zengwangfa/Smart-Hive/software/node-2019.10.29/docs/A Low-Power CoAP for Contiki.ppt.pdf

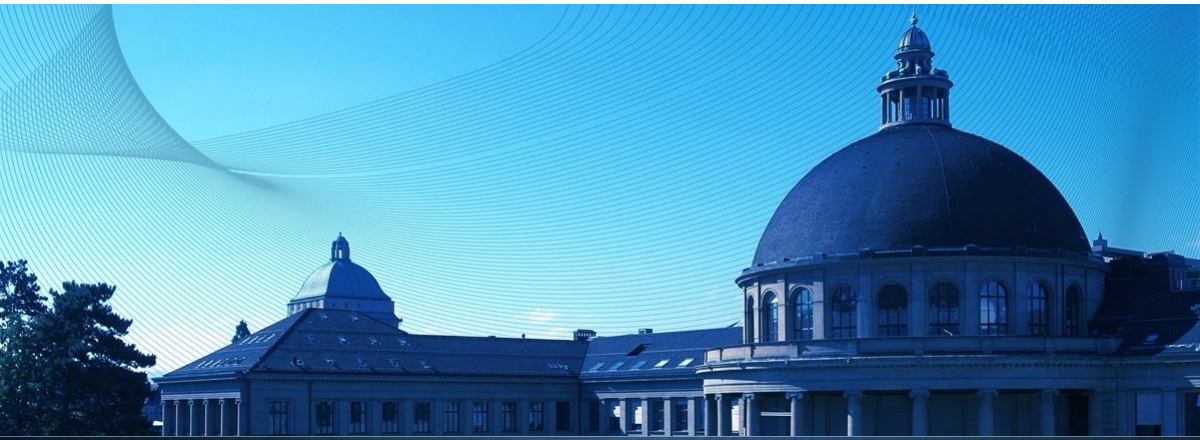
[picture p32: figure]

Monday, 17 Oct 2011

# A Low-Power CoAP for Contiki

### Matthias Kovatsch, Simon Duquennoy, and Adam Dunkels

kovatsch@inf.ethz.ch | simonduq@sics.se | adam@sics.se

Matthias Kovatsch – ETH Zürich | A Low-Power CoAP for Contiki

## Internet of Things Protocol Stack

Layer | Protocol

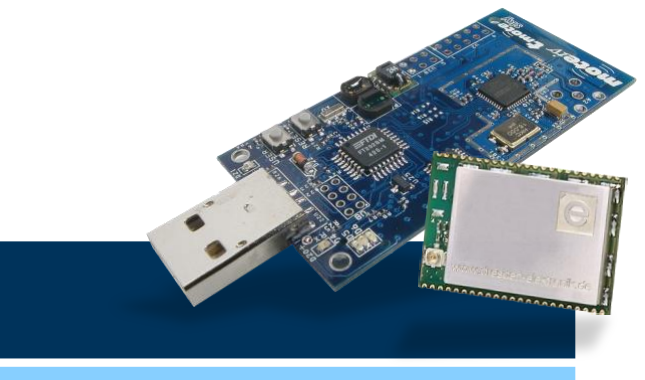
[picture p33: figure]

Application | CoAP / REST Engine (Erbium)
Transport | UDP
Network | IPv6 / RPL
Adaption | 6LoWPAN
MAC | CSMA / link-layer bursts / link-layer bursts
Radio Duty Cycling | ContikiMAC
Physical | IEEE 802.15.4

## ContikiMAC

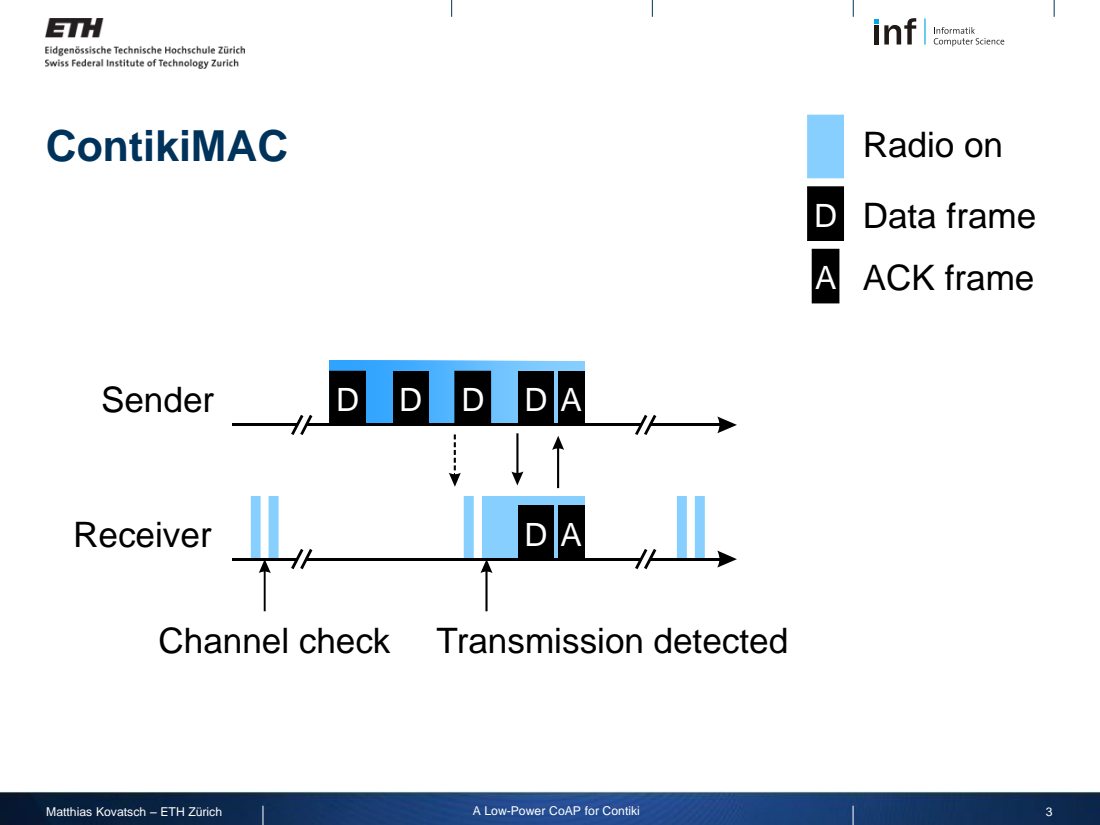
[picture p34: page 3]
ACK frame; Data frame; Radio on; Sender; Receiver; Transmission detected; Channel check

## Link-layer Bursts

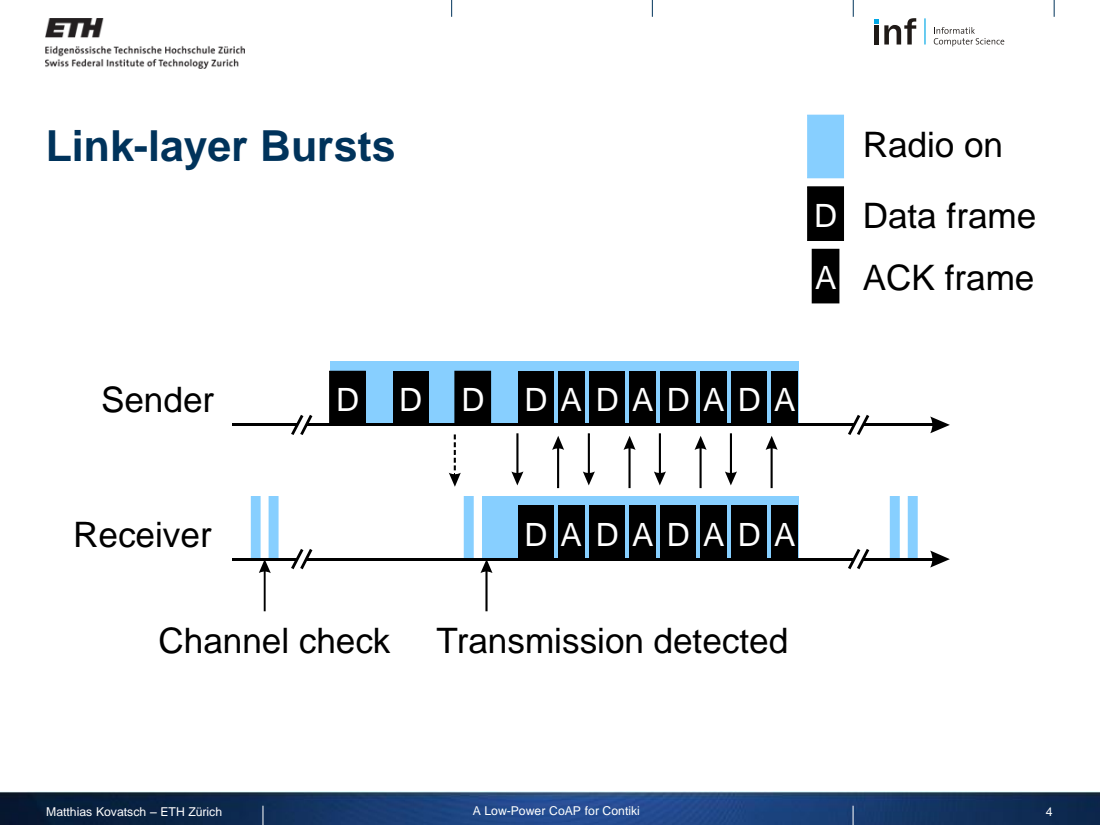
[picture p35: page 4]
Sender; Receiver; Transmission detected; Channel check; A ACK frame; Data frame; Radio on

## Constrained Application Protocol (CoAP)

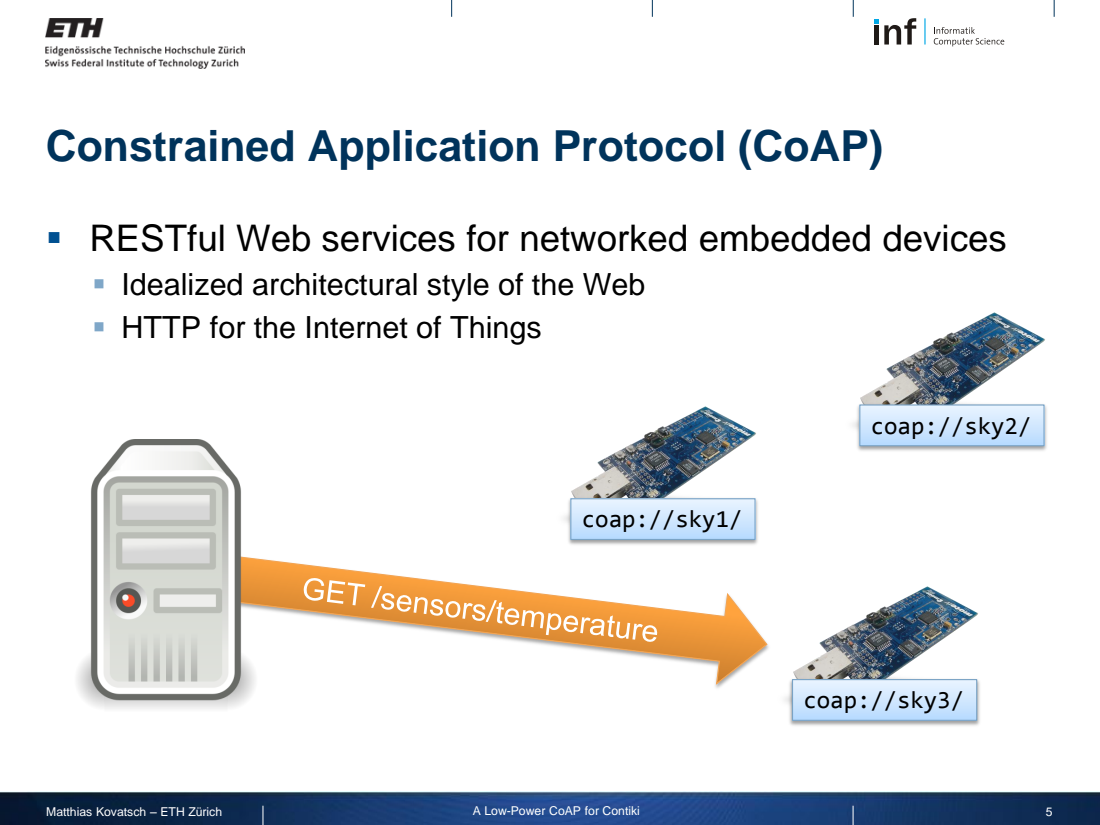
[picture p36: page 5]
coap://sky3/; coap://sky2/; coap://sky1/

▪ RESTful Web services for networked embedded devices
▪ Idealized architectural style of the Web
▪ HTTP for the Internet of Things

## «Erbium» CoAP for Contiki

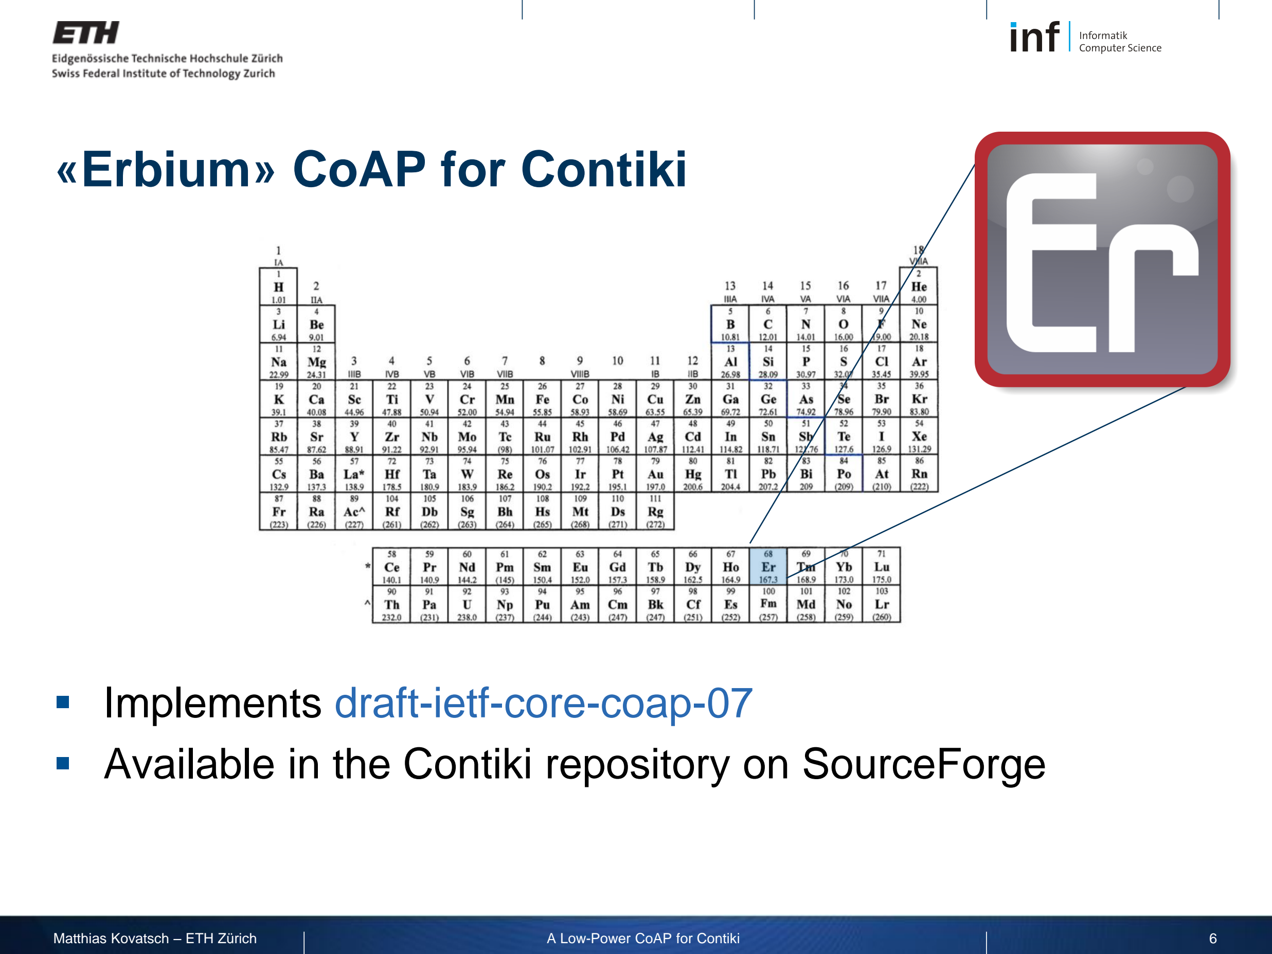
[picture p37: page 6]

### - Implements draft-ietf-core-coap-07 - Available in the Contiki repository on SourceForge

## «Erbium» CoAP

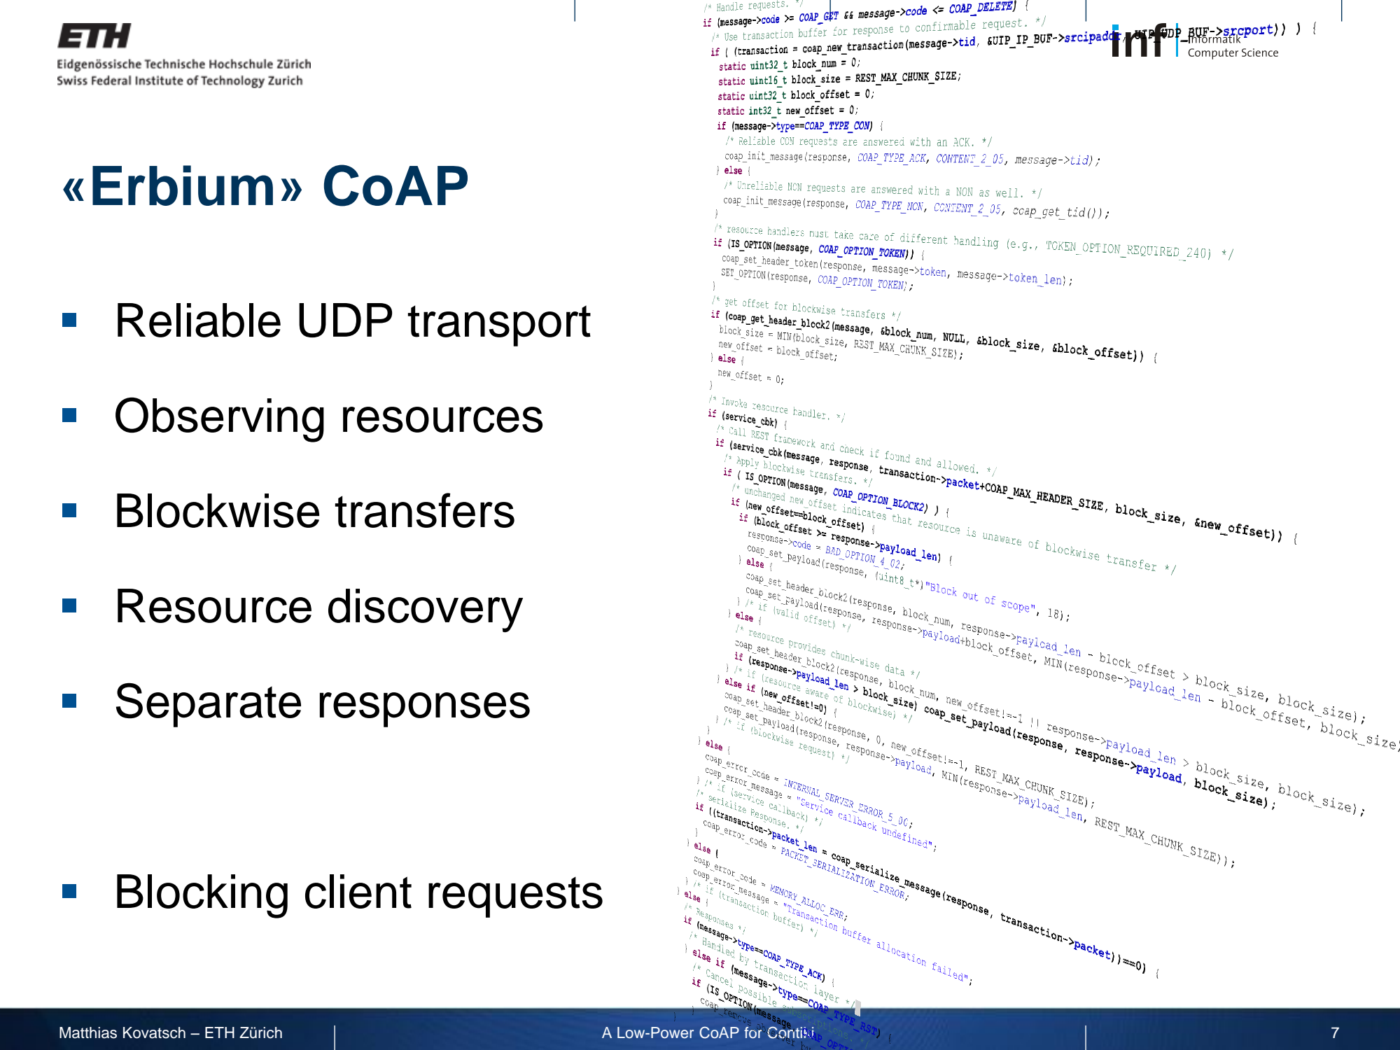
[picture p38: page 7]

### - Reliable UDP transport

### - Observing resources

### - Blockwise transfers

### - Resource discovery

### - Separate responses

### - Blocking client requests

## «Erbium» REST Engine

### - Resource abstraction

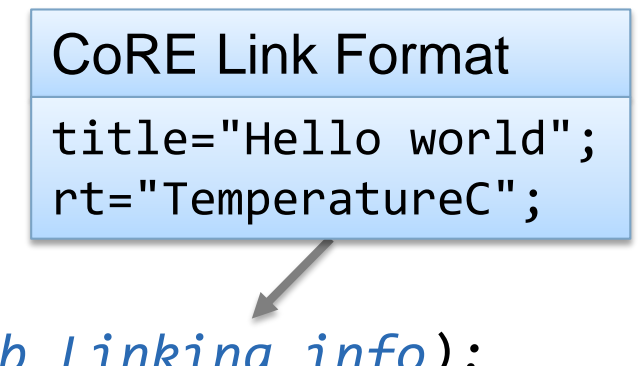
[picture p39: figure]
CoRE Link Format; title="Hello world"; rt="TemperatureC";

RESOURCE(handle, METHODs, URI-Path, Web Linking info);
- Resource handler

PERIODIC_RESOURCE(handle, METHODs, URI-Path, info, period);
- Additional periodic handler

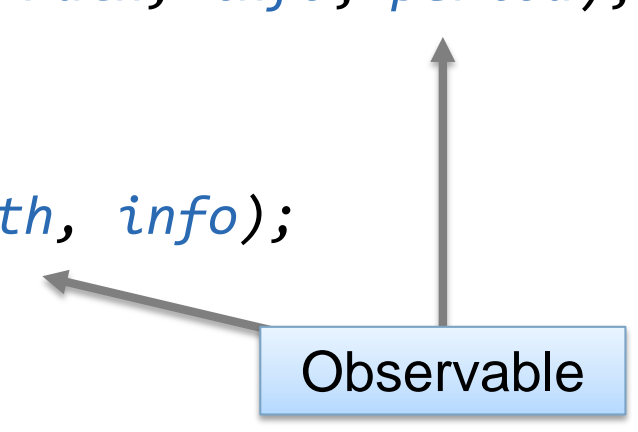
[picture p40: figure]
Observable

EVENT_RESOURCE(handle, METHODs, URI-Path, info);
- Additional event handler

## «Erbium» Memory Footprint

| ROM [kB] | RAM [kB]
CoAP REST Engine total | 8.5 | 1.5
Measured stack usage | – | 0.1
REST Engine | 0.7 | 0
CoAP-07 base | 4.5 | 0
CoAP-07 server | 1.9 | 0.3
CoAP-07 transport | 0.4 | 0.9
CoAP-07 observing | 0.9 | 0.2
CoAP-07 separate | 0.1 | 0

## Experimental Set-up

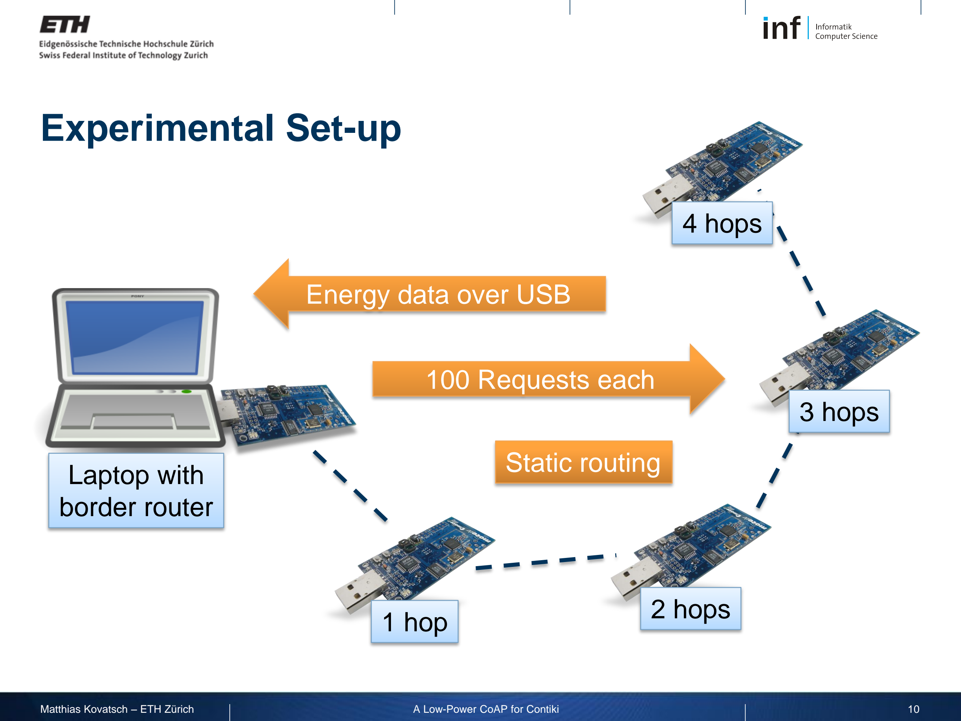
[picture p41: page 10]

3 hops

2 hops 1 hop

Energy data over USB

100 Requests each

Laptop with
border router

Static routing

4 hops

## Energy vs Latency for 64B Payload

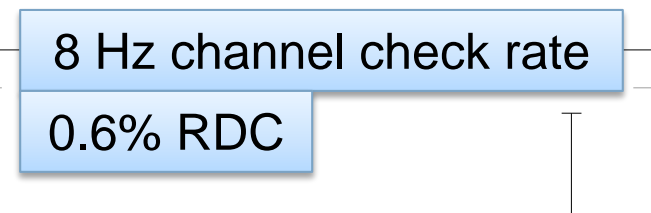
[picture p42: figure]
8 Hz channel check rate; 0.6% RDC

Number of hops | Number of hops

Energy [mJ]
Latency [s]

No duty cycling
ContikiMAC
1 | 2 | 3 | 4

0

100

200

300

400

1 | 2 | 3 | 4

0

0.2

0.4

0.6

0.8

1.0

## Transmitting Large Data

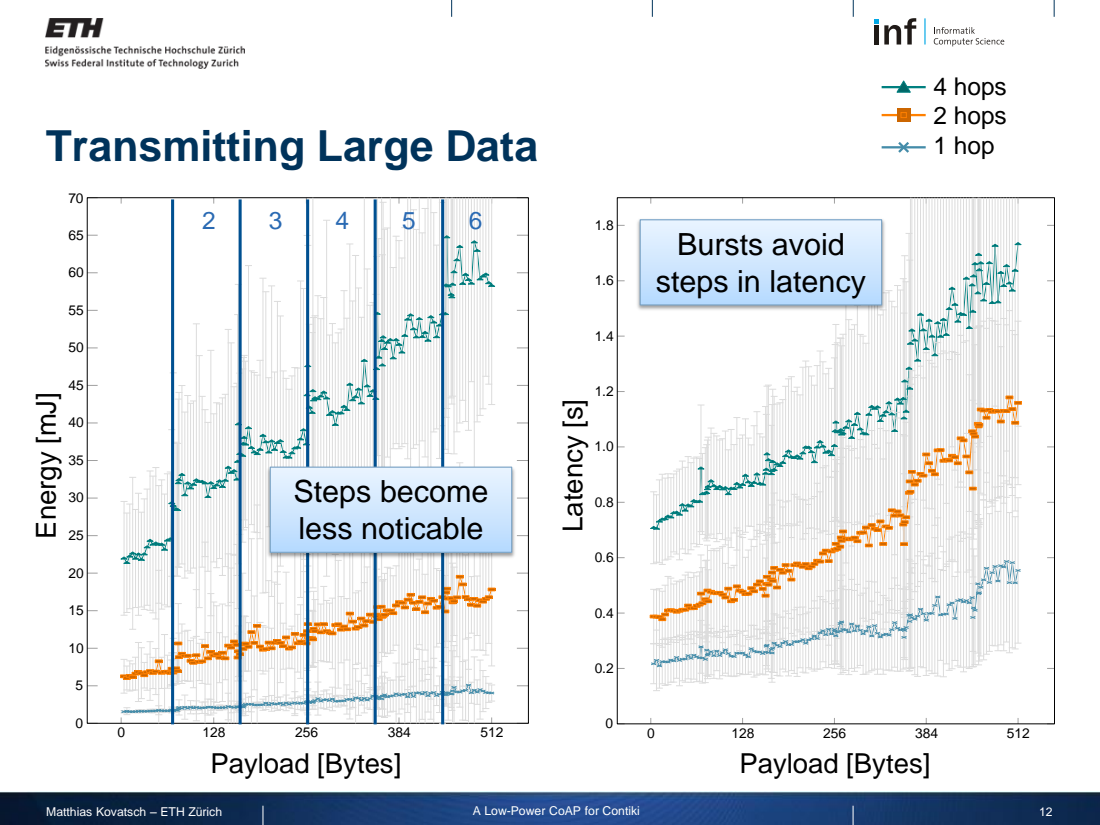
[picture p43: page 12]
Payload [Bytes]; Energy [mJ]; Latency [s]; Steps become less noticable; 4 hops 2 hops 1 hop

Bursts avoid
steps in latency

## Transmitting Large Data

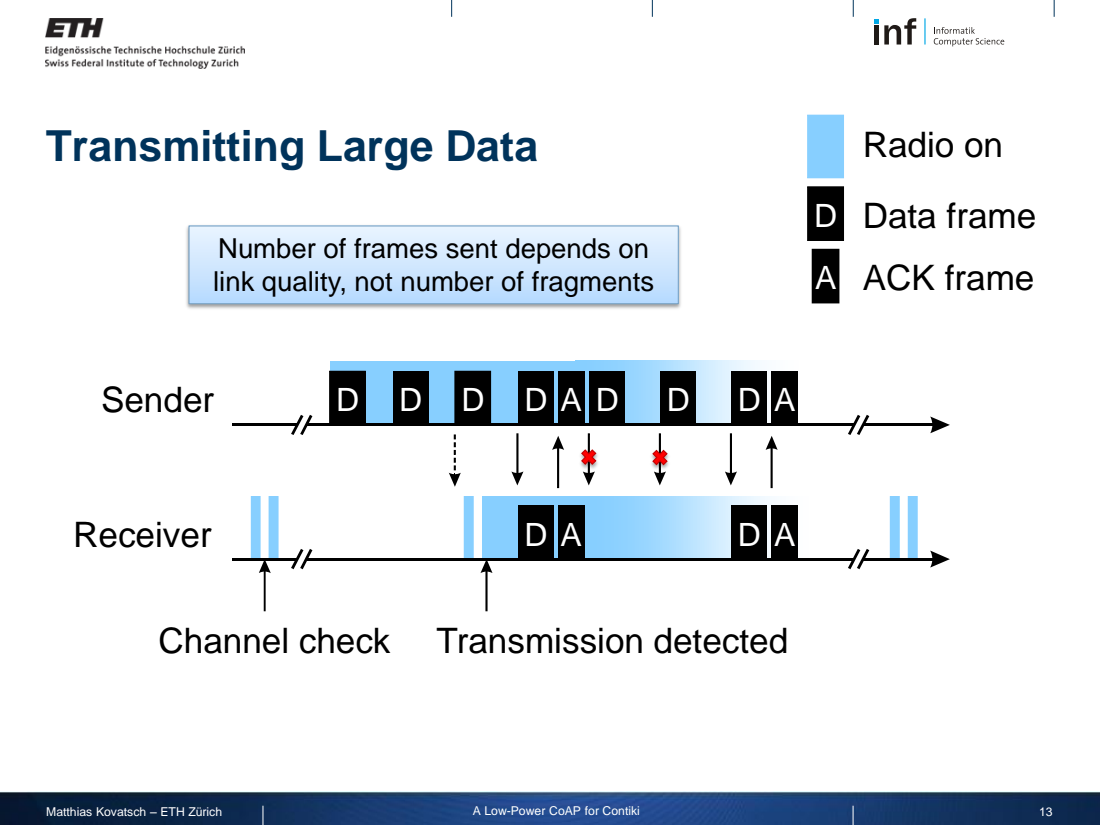
[picture p44: page 13]
Sender; Receiver; Transmission detected; Channel check; A ACK frame; Data frame; Radio on

Number of frames sent depends on
link quality, not number of fragments

## Separate Responses

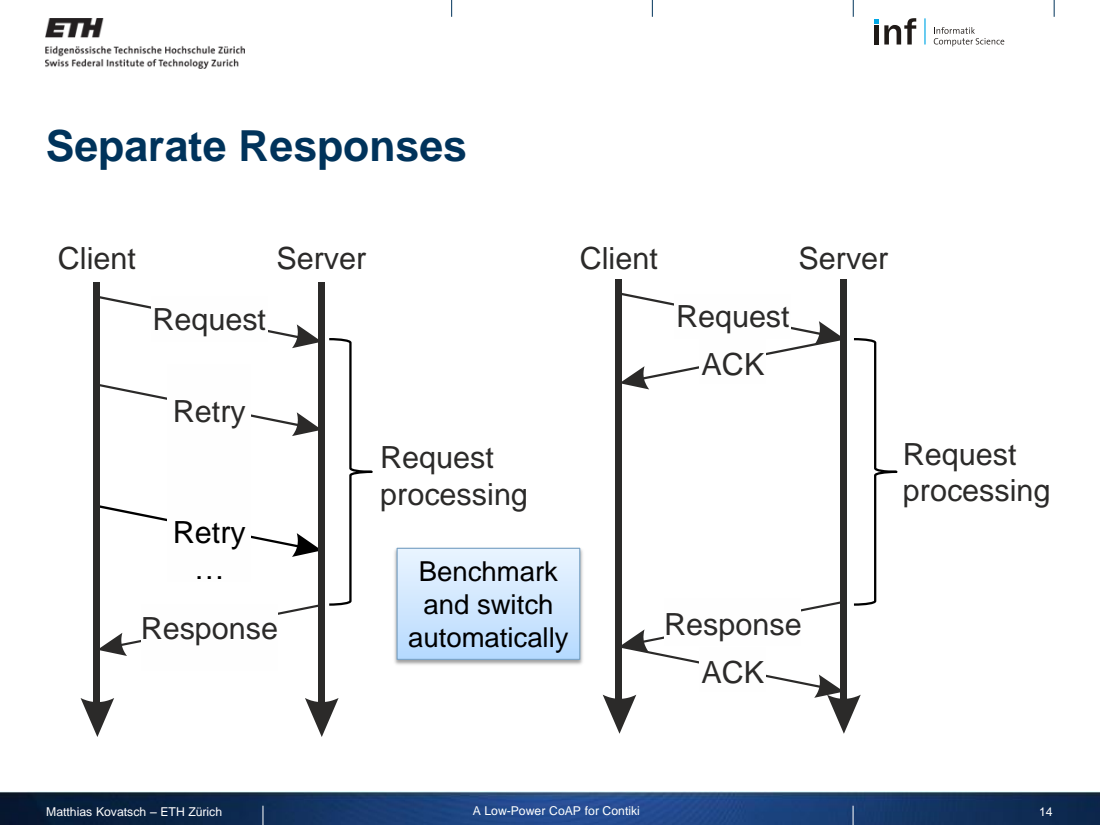
[picture p45: page 14]
Client; Server; Request processing; Request; Retry; Retry …; Response; ACK; Benchmark and switch automatically

## Separate Responses over 4 Hops

Without
With

Energy [mJ]

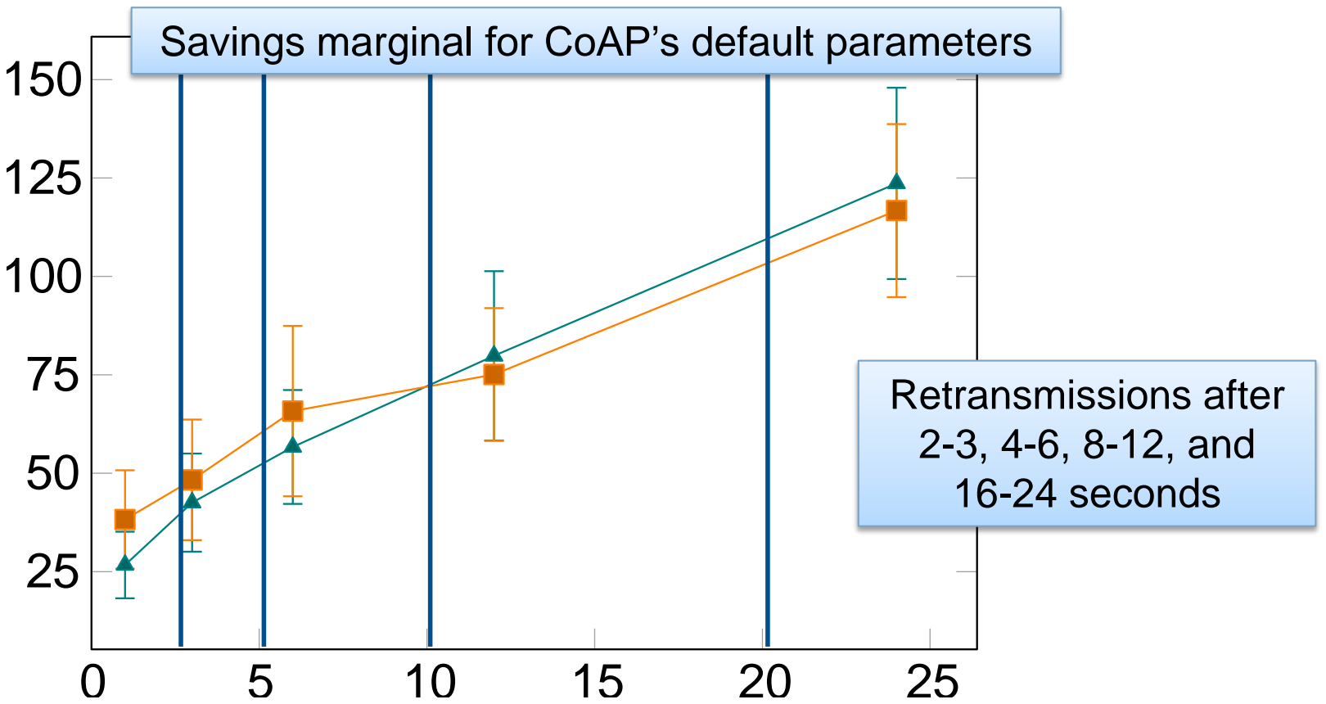
[picture p46: figure]
Retransmissions after 2-3, 4-6, 8-12, and 16-24 seconds

Server processing time [s]

Savings marginal for CoAP’s default parameters

## Conclusion

### - Internet of Things stack

- Isolated layers with different goals work together
- Layered architecture lowers complexity
- Optimize for single fragments
- No need to optimize payload size once fragmented

### - CoAP

- Draft 07 implementation for Contiki
- Block size most important parameter for memory-constrained devices: Exponential sizes too coarse-grained

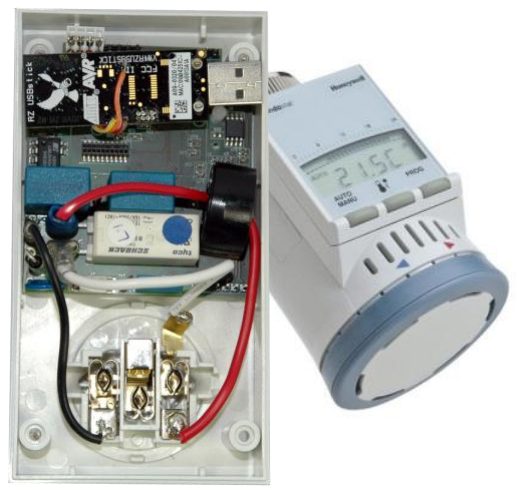
[picture p47: figure]

## Future Work

### - Extend «Erbium» CoAP

- Blocking resource handler for UART
- Hierarchical resources / URI-Path handling
- Improve observer handling (only one buffer)

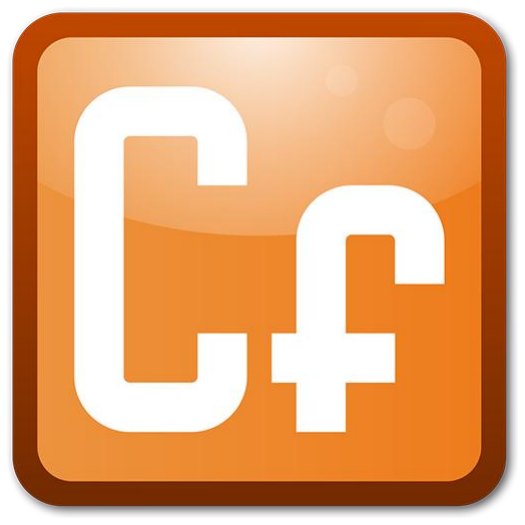
[picture p48: figure]

### - Study RESTful approach

- Long-term deployment with smart appliances
- Separate application logic from device firmware and combine with «Californium»-based App Server

https://github.com/mkovatsc/Californium

## THANK YOU

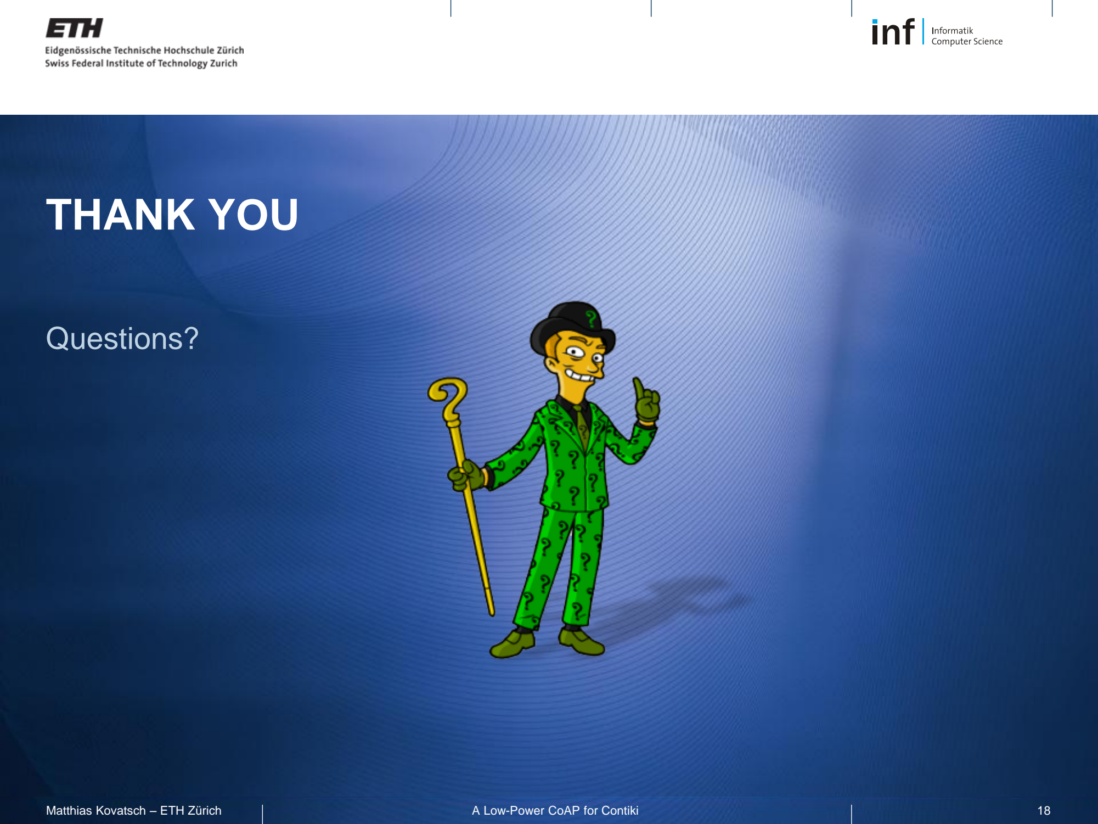
[picture p49: page 18]

Questions?

## Blockwise Transfers

### Automatic or controlled by handler

RESOURCE(handle, METHODs, URI-Path, Web Linking info);
- Resource handler

handle_handler(void* request, void* response,
uint8_t *buffer, uint16_t preferred_size, int32_t *offset);

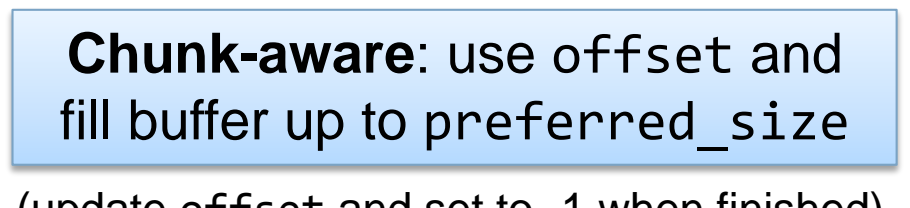
[picture p50: figure]
Chunk-aware: use offset and fill buffer up to preferred_size
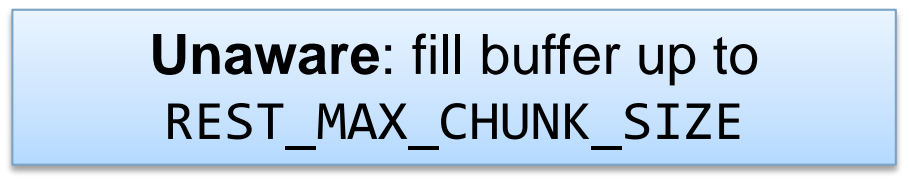
[picture p51: figure]
Unaware: fill buffer up to REST_MAX_CHUNK_SIZE

(update offset and set to -1 when finished)

## Observing Resources

### Post-handler registers observers automatically

PERIODIC_RESOURCE(handle, METHODs, URI-Path, info, period);
- Additional periodic handler

EVENT_RESOURCE(handle, METHODs, URI-Path, info);
- Additional event handler

int handle_event_handler(resource_t *r) {
REST.notify_subscribers(r->url, CON/NON, seqno, buf, len); }

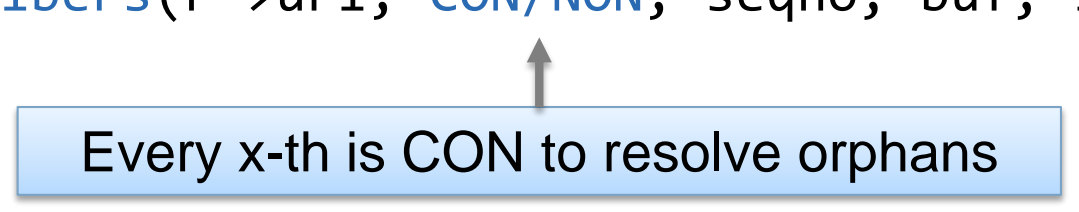
[picture p52: figure]
Every x-th is CON to resolve orphans

## «Erbium» REST Engine

### - Manipulate messages with REST API

- REST.set_header_etag(response, etag_buf, etag_len);
- REST.get_query_variable(request, name, value_buffer);

### - Link implementation

- coap-03
- coap-06
- coap-07
- …
- HTTP (not yet implemented for Erbium)
