zengwangfa/Smart-Hive/docs/网关使用说明/蜂箱网关使用简要说明.pdf

网关设备使用简要说明

## 一、供电

供电注意：使用5V电源适配器供电

## 二、联网

在网关设备网口处出入可直接上网的网线即可

## 三、使用方法

将网关部署在距离蜂箱节点附近，即可让蜂箱
节点自动上传数据至服务器，并可下行控制蜂
箱节点执行相应动作。

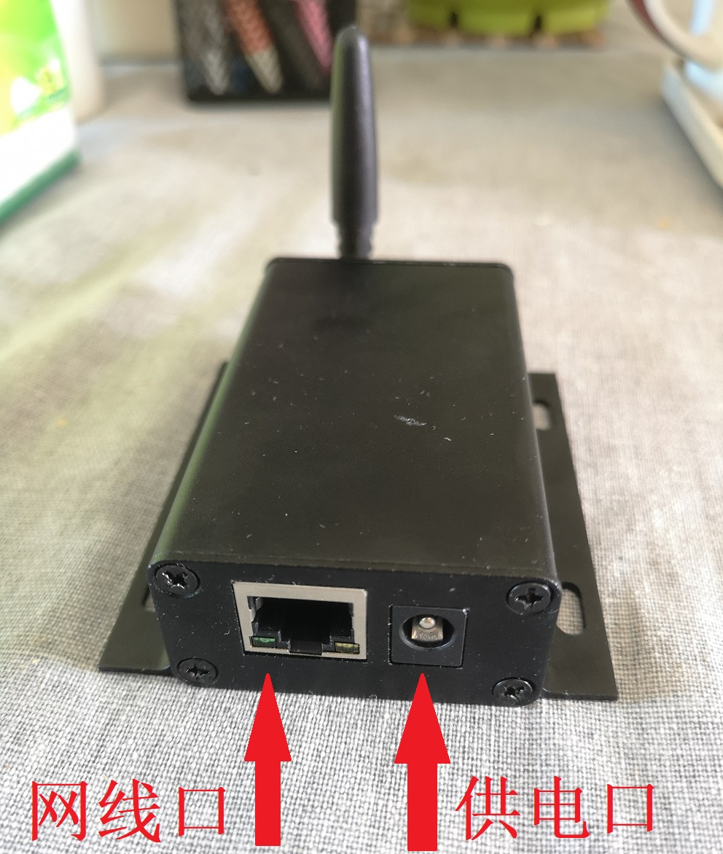
[picture p64: figure]
