zengwangfa/Smart-Hive/docs/pictures/uboot.png

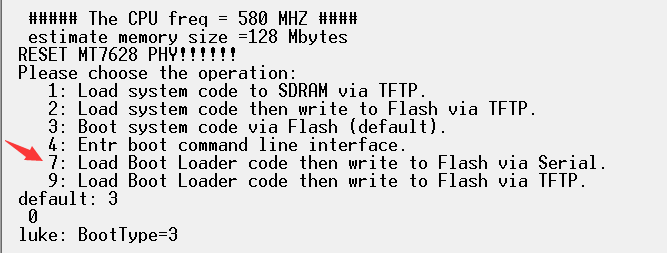
docs/pictures/uboot.png
