zengwangfa/Smart-Hive/new_node/bsp/stm32/docs/figures/adc_config3.png

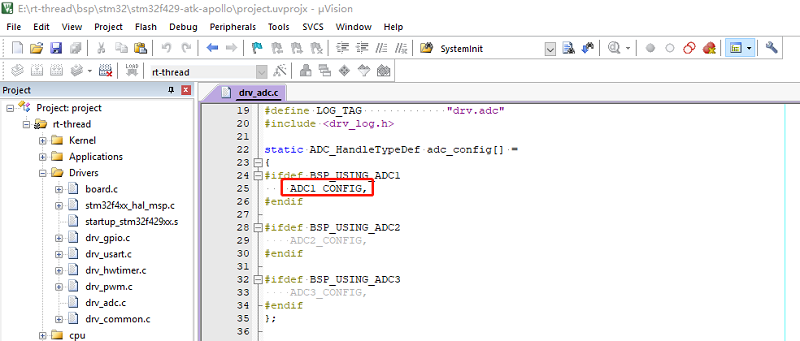
new_node/bsp/stm32/docs/figures/adc_config3.png
