zengwangfa/Smart-Hive/new_node/bsp/stm32/docs/figures/board_1.png

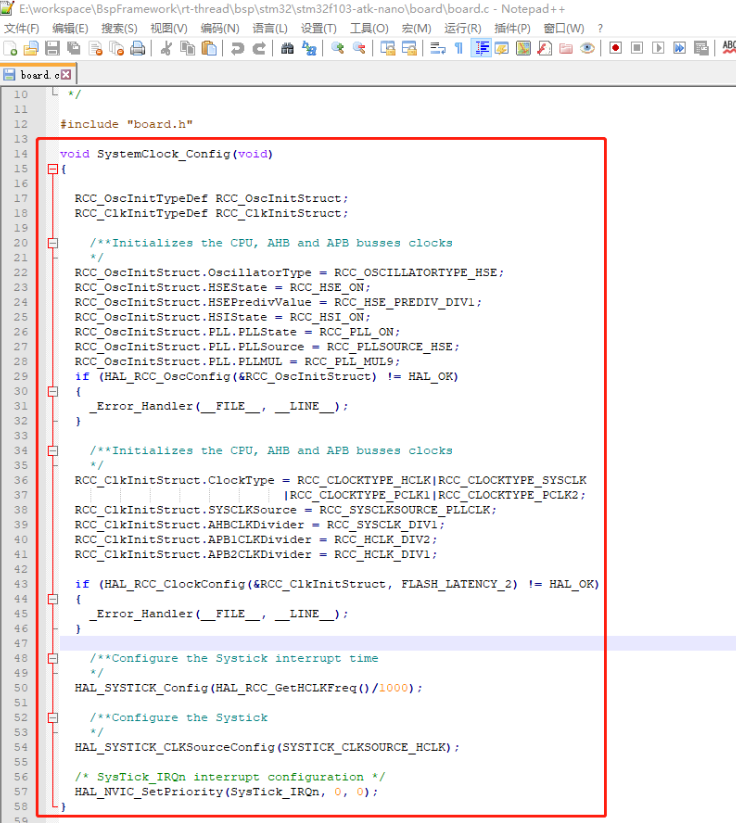
new_node/bsp/stm32/docs/figures/board_1.png
