zengwangfa/Smart-Hive/new_node/bsp/stm32/docs/figures/board_h.png

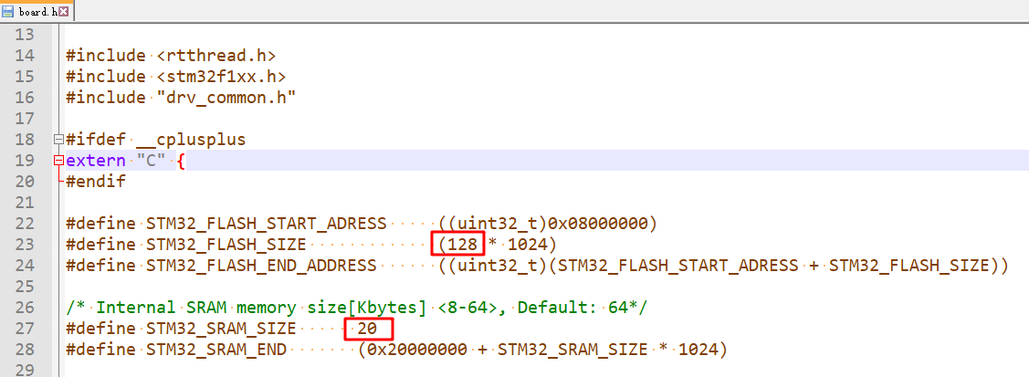
new_node/bsp/stm32/docs/figures/board_h.png
