zengwangfa/Smart-Hive/new_node/bsp/stm32/docs/figures/bsp_template_dir.png

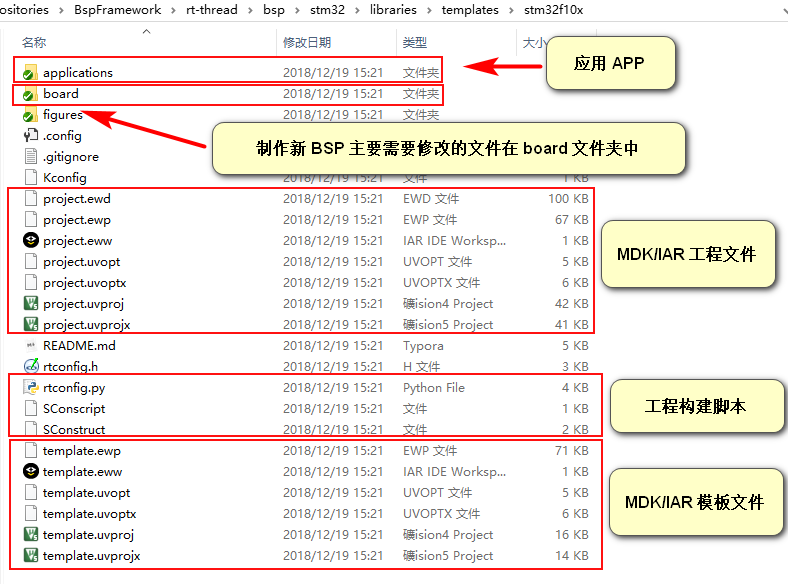
new_node/bsp/stm32/docs/figures/bsp_template_dir.png
