zengwangfa/Smart-Hive/new_node/bsp/stm32/docs/figures/complise.png

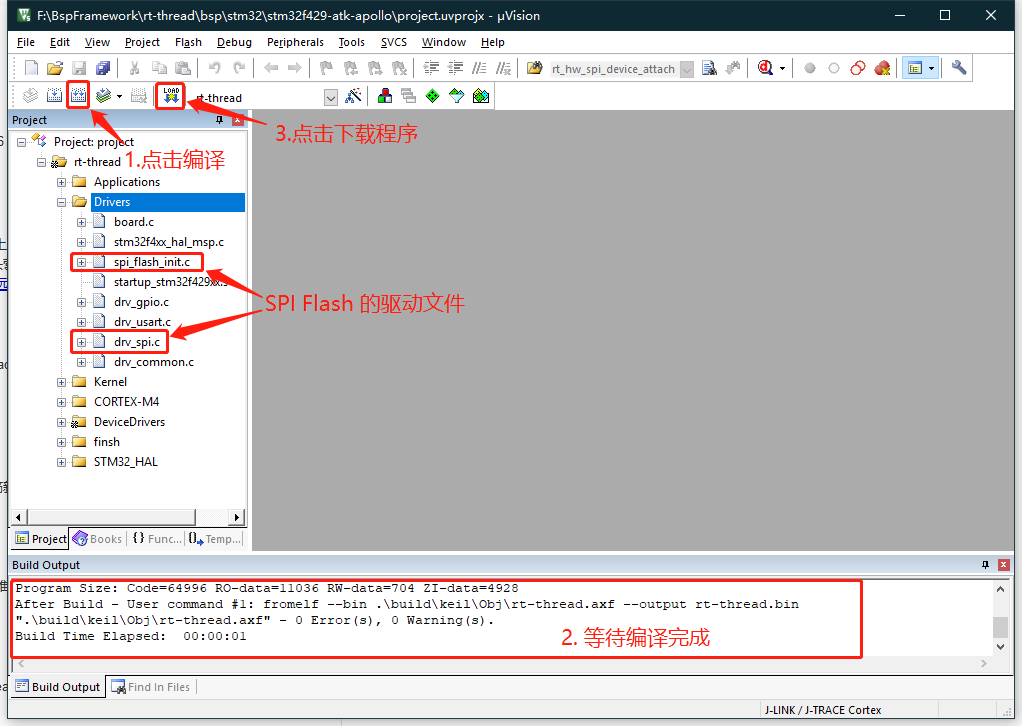
new_node/bsp/stm32/docs/figures/complise.png
