zengwangfa/Smart-Hive/new_node/bsp/stm32/docs/figures/config1.png

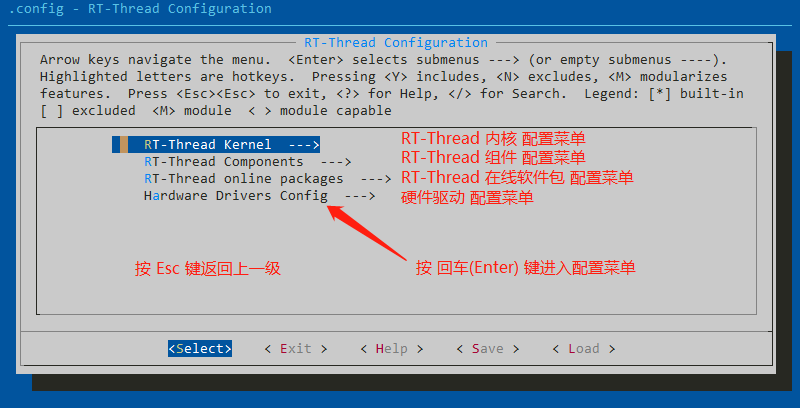
new_node/bsp/stm32/docs/figures/config1.png
