zengwangfa/Smart-Hive/new_node/bsp/stm32/docs/figures/config2.png

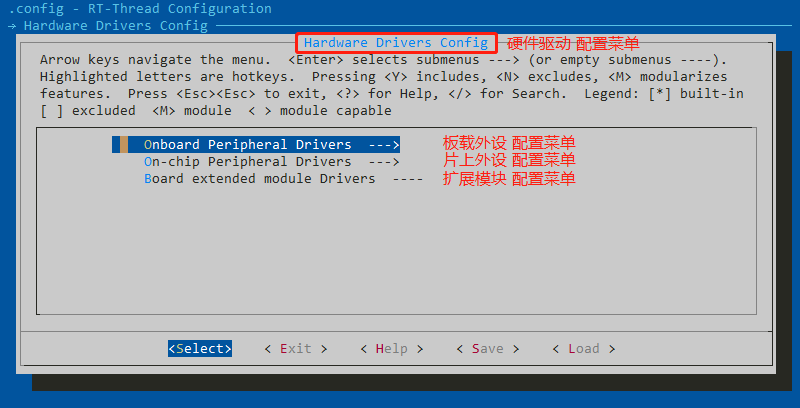
new_node/bsp/stm32/docs/figures/config2.png
