zengwangfa/Smart-Hive/new_node/bsp/stm32/docs/figures/config4.png

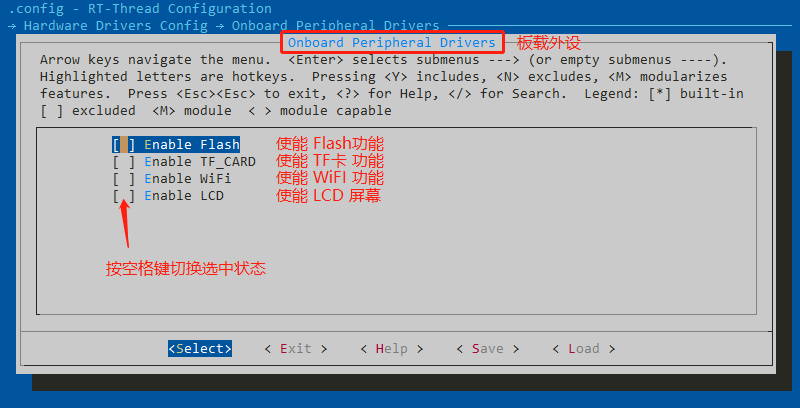
new_node/bsp/stm32/docs/figures/config4.png
