zengwangfa/Smart-Hive/new_node/bsp/stm32/docs/figures/config5.png

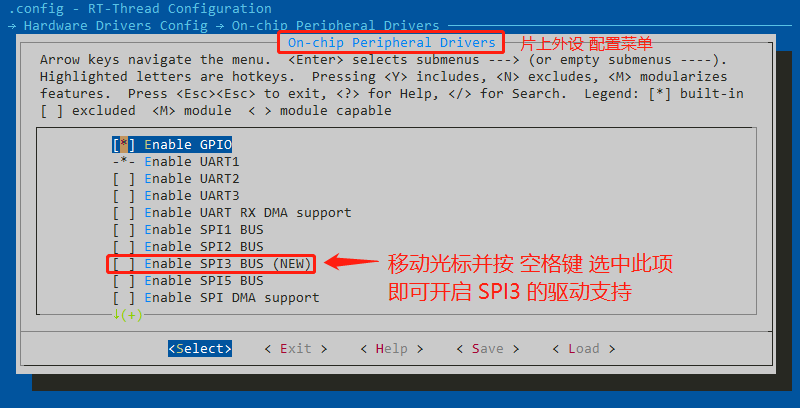
new_node/bsp/stm32/docs/figures/config5.png
