zengwangfa/Smart-Hive/new_node/bsp/stm32/docs/figures/config.png

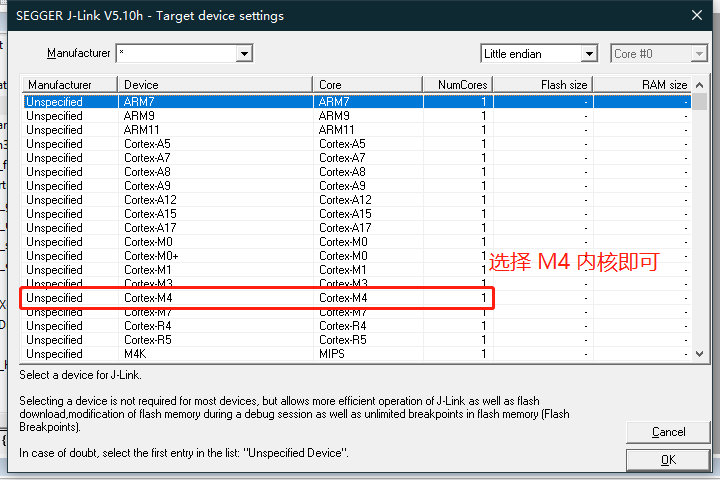
new_node/bsp/stm32/docs/figures/config.png
