zengwangfa/Smart-Hive/new_node/bsp/stm32/docs/figures/cube_spi3.png

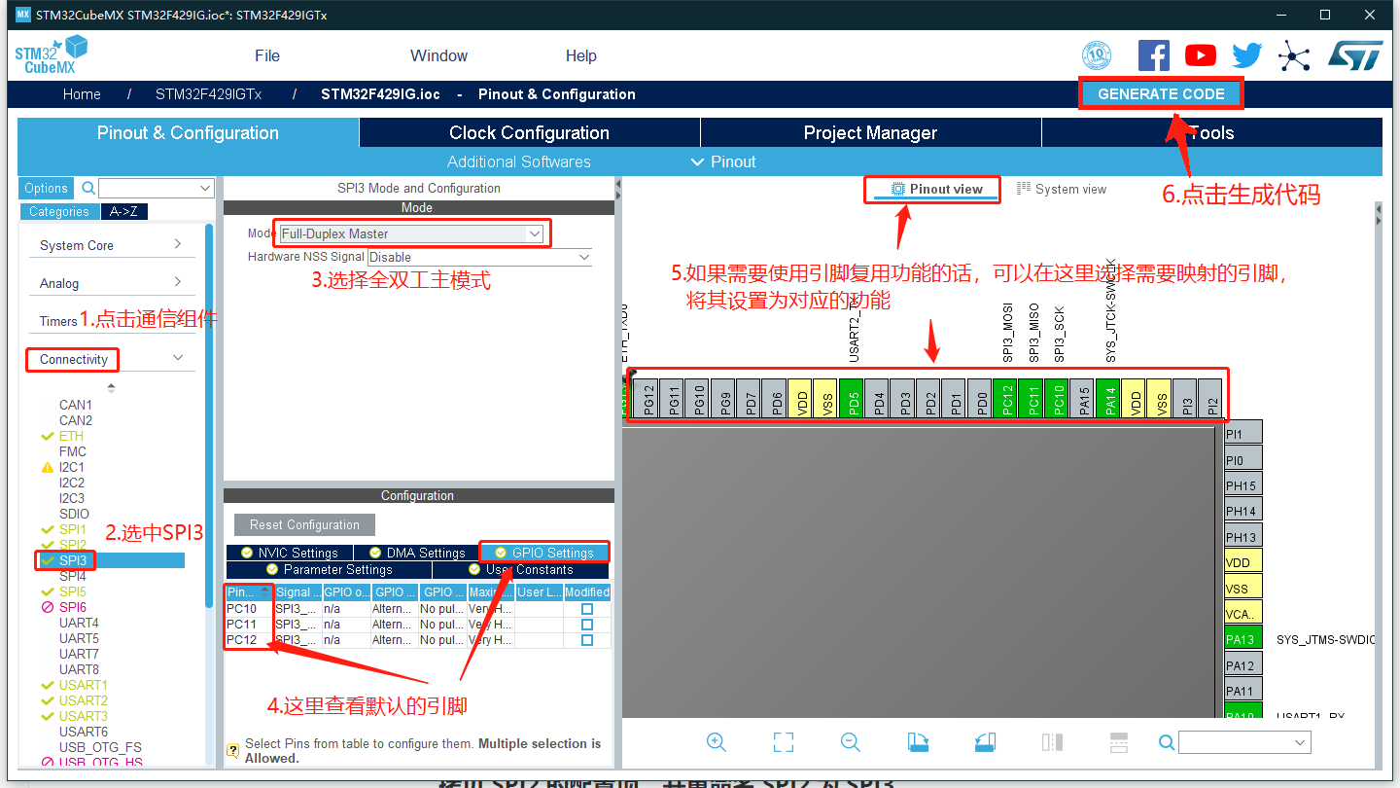
new_node/bsp/stm32/docs/figures/cube_spi3.png
