zengwangfa/Smart-Hive/new_node/bsp/stm32/docs/figures/cubemx.png

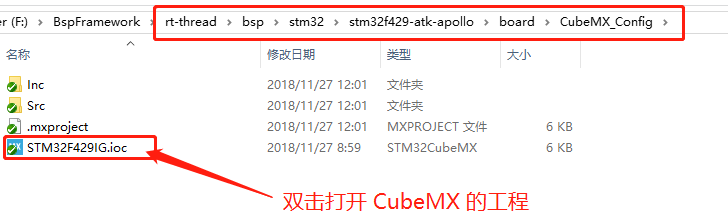
new_node/bsp/stm32/docs/figures/cubemx.png
