zengwangfa/Smart-Hive/new_node/bsp/stm32/docs/figures/CubeMX_2.png

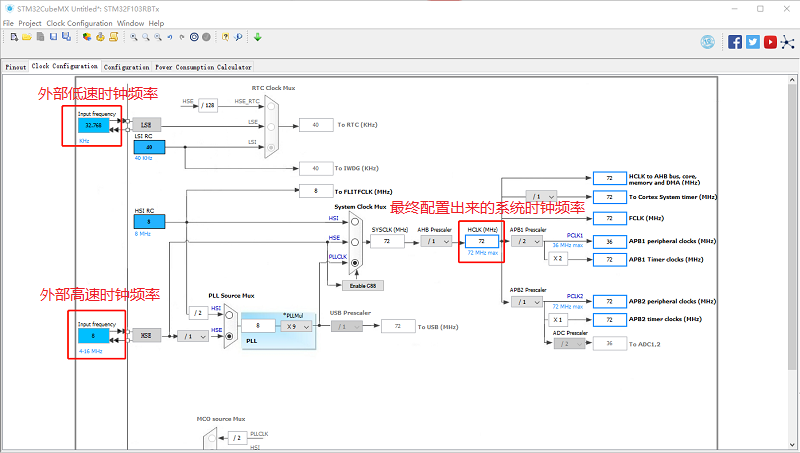
new_node/bsp/stm32/docs/figures/CubeMX_2.png
