zengwangfa/Smart-Hive/new_node/bsp/stm32/docs/figures/CubeMX_3.png

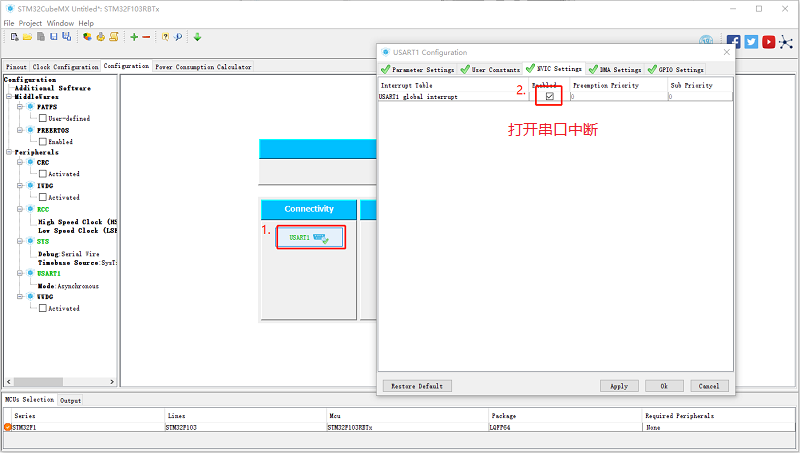
new_node/bsp/stm32/docs/figures/CubeMX_3.png
