zengwangfa/Smart-Hive/new_node/bsp/stm32/docs/figures/exit.png

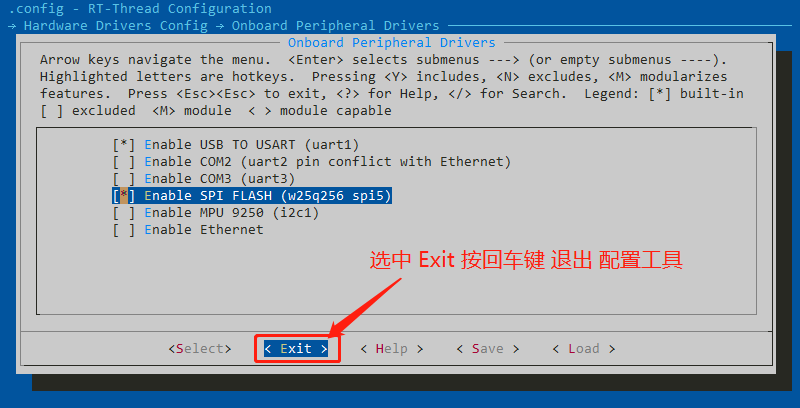
new_node/bsp/stm32/docs/figures/exit.png
