zengwangfa/Smart-Hive/new_node/bsp/stm32/docs/figures/frame.png

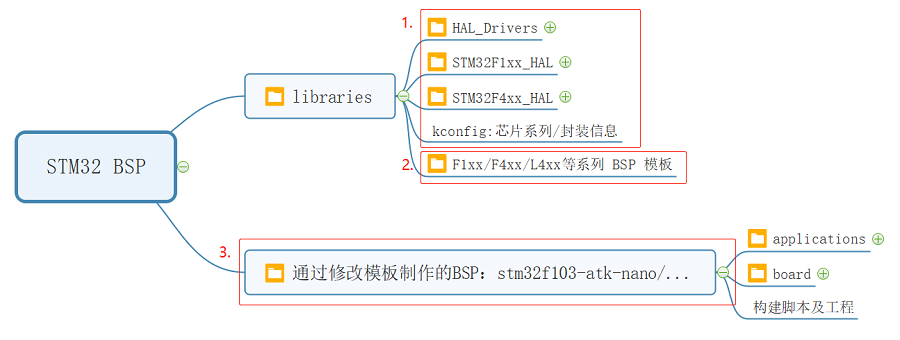
new_node/bsp/stm32/docs/figures/frame.png
