zengwangfa/Smart-Hive/new_node/bsp/stm32/docs/figures/heap_config.png

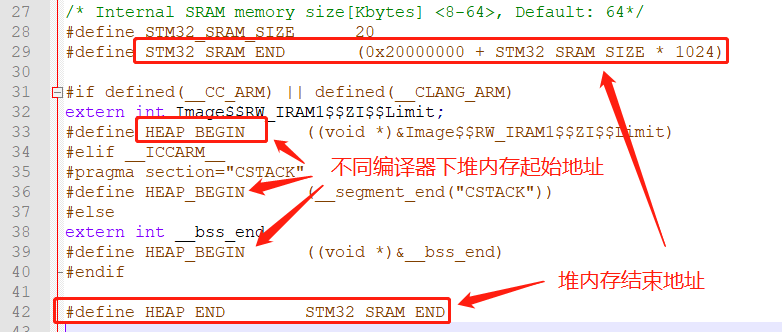
new_node/bsp/stm32/docs/figures/heap_config.png
