zengwangfa/Smart-Hive/new_node/bsp/stm32/docs/figures/Kconfig2.png

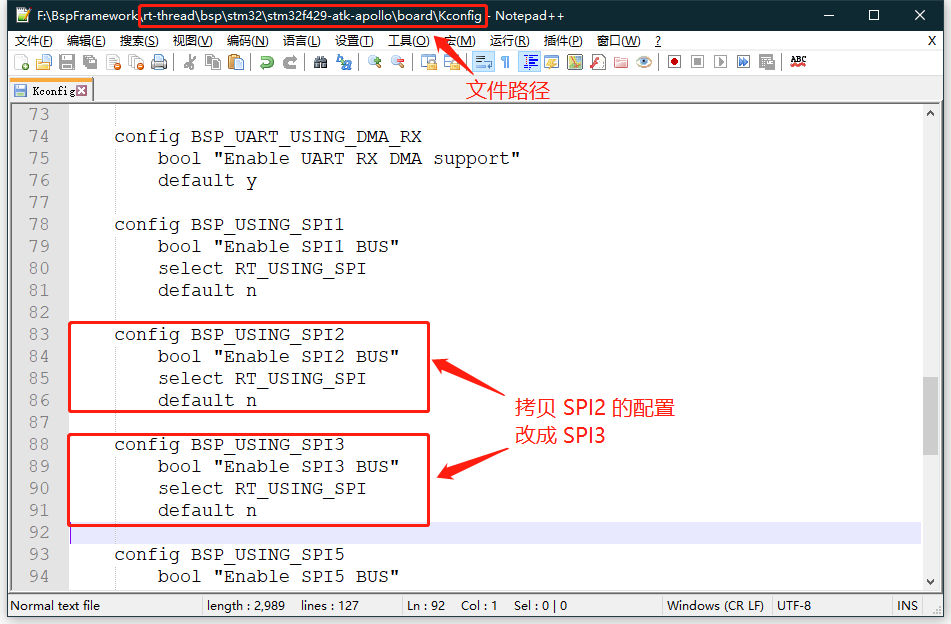
new_node/bsp/stm32/docs/figures/Kconfig2.png
