zengwangfa/Smart-Hive/new_node/bsp/stm32/docs/figures/Kconfig.png

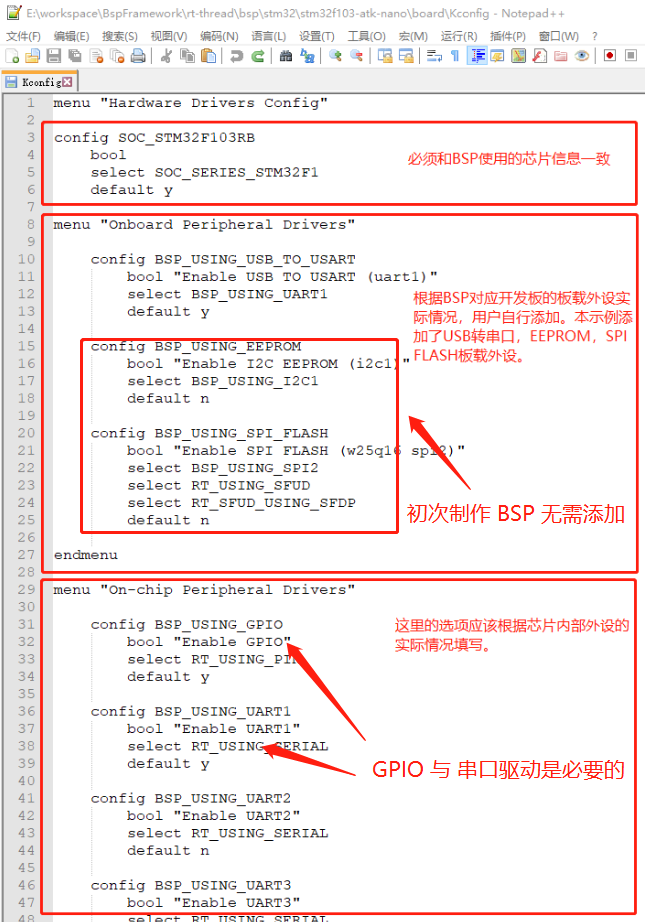
new_node/bsp/stm32/docs/figures/Kconfig.png
