zengwangfa/Smart-Hive/new_node/bsp/stm32/docs/figures/link_icf.png

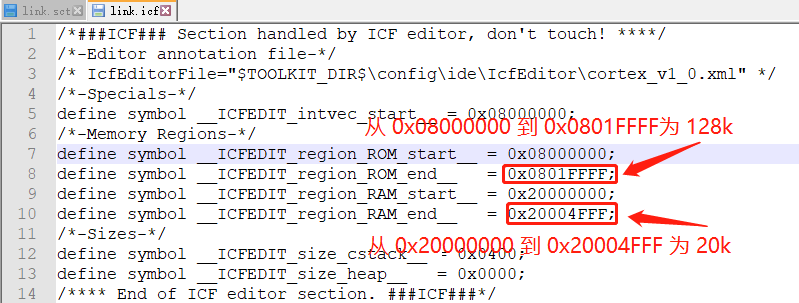
new_node/bsp/stm32/docs/figures/link_icf.png
