zengwangfa/Smart-Hive/new_node/bsp/stm32/docs/figures/link_lds.png

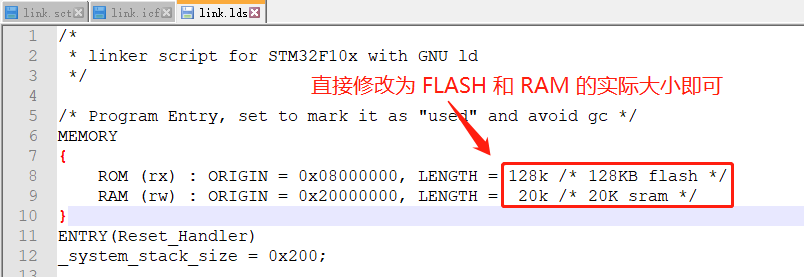
new_node/bsp/stm32/docs/figures/link_lds.png
