zengwangfa/Smart-Hive/new_node/bsp/stm32/docs/figures/linkscripts_change.png

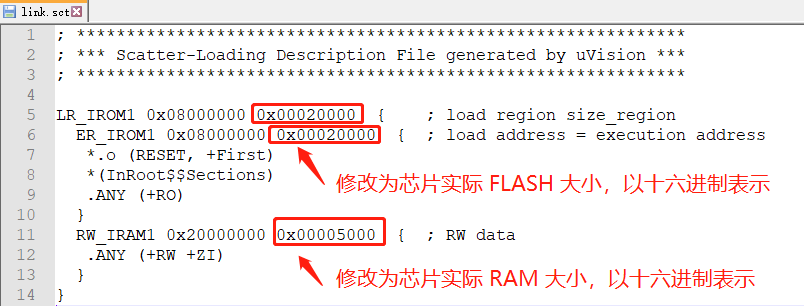
new_node/bsp/stm32/docs/figures/linkscripts_change.png
