zengwangfa/Smart-Hive/new_node/bsp/stm32/docs/figures/menuconfig.png

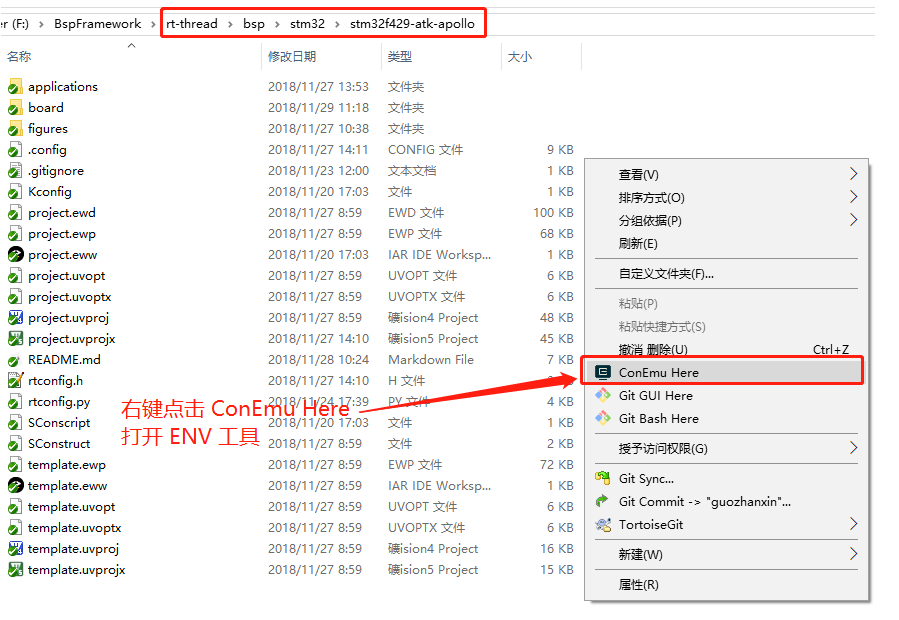
new_node/bsp/stm32/docs/figures/menuconfig.png
