zengwangfa/Smart-Hive/new_node/bsp/stm32/docs/figures/menuconfig_2.png

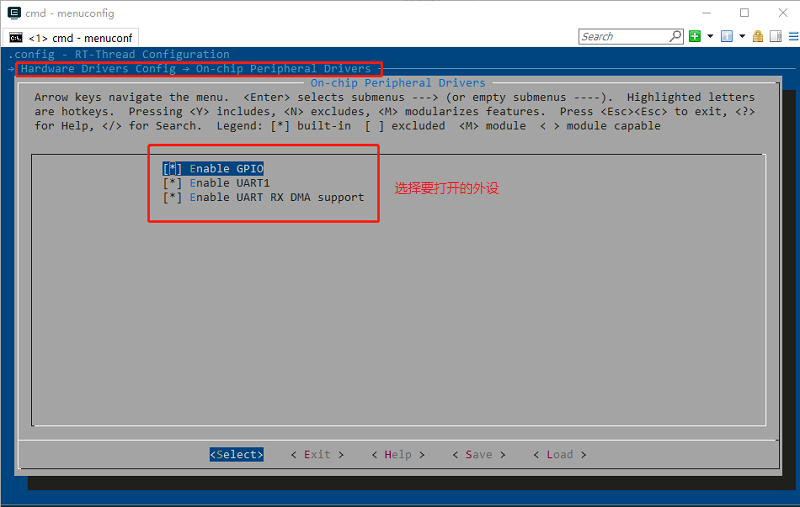
new_node/bsp/stm32/docs/figures/menuconfig_2.png
