zengwangfa/Smart-Hive/new_node/bsp/stm32/docs/figures/on_chip_config.png

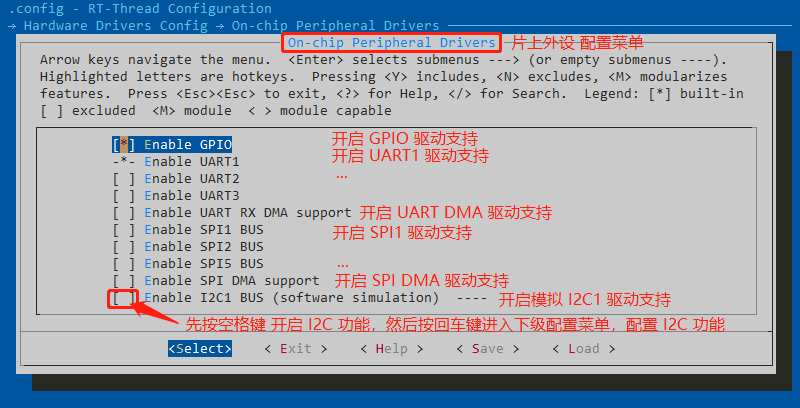
new_node/bsp/stm32/docs/figures/on_chip_config.png
