zengwangfa/Smart-Hive/new_node/bsp/stm32/docs/figures/Peripheral.png

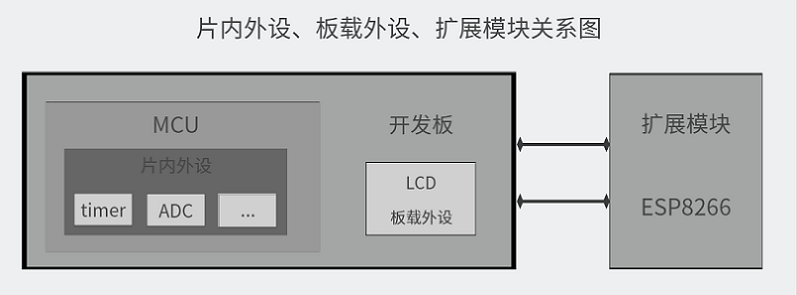
new_node/bsp/stm32/docs/figures/Peripheral.png
