zengwangfa/Smart-Hive/new_node/bsp/stm32/docs/figures/pulse_encoder_config1.png

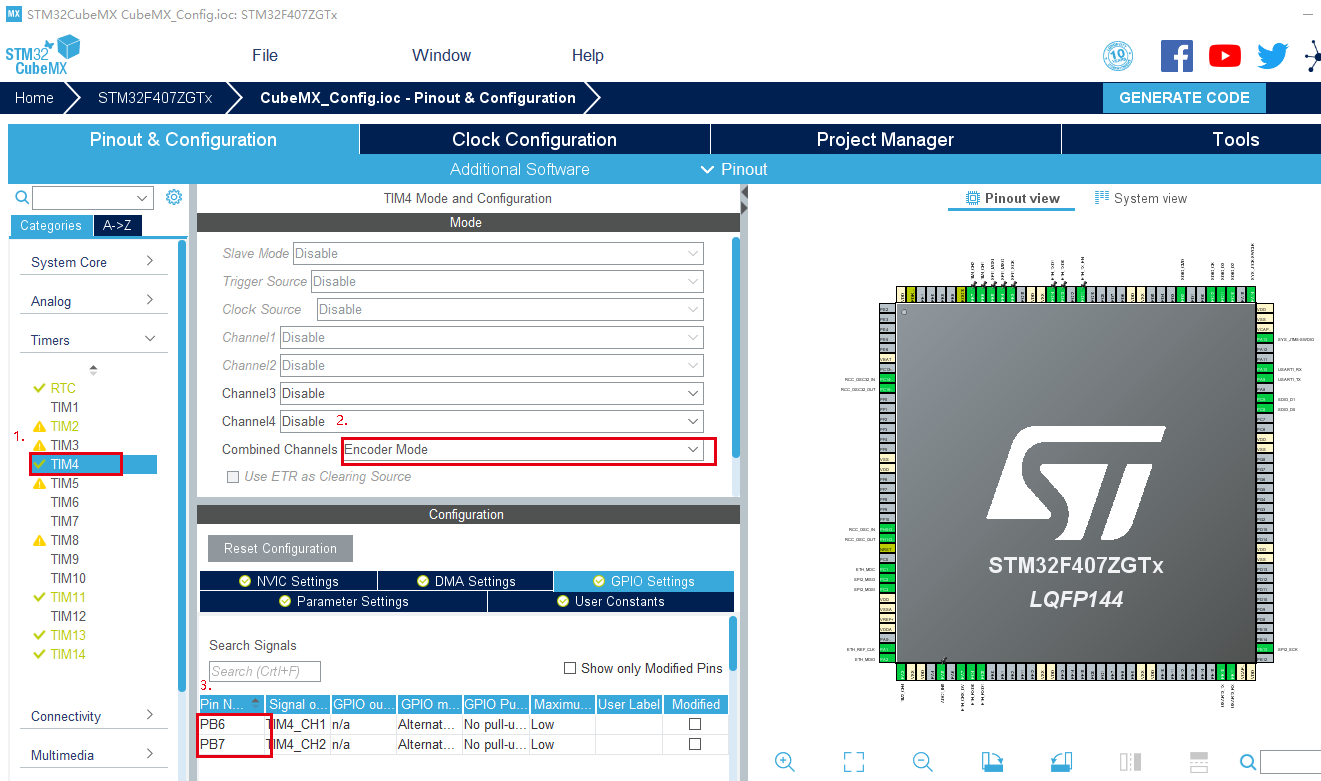
new_node/bsp/stm32/docs/figures/pulse_encoder_config1.png
