zengwangfa/Smart-Hive/new_node/bsp/stm32/docs/figures/rt_device.png

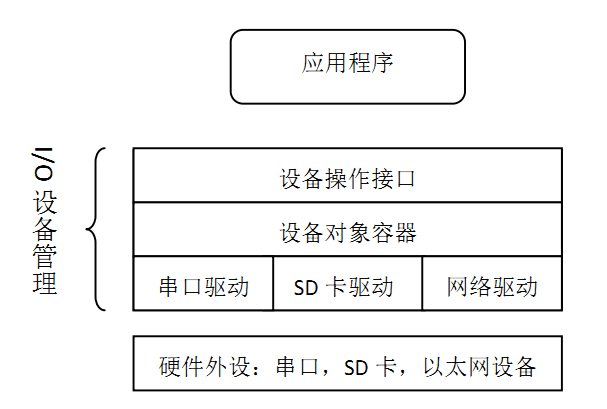
new_node/bsp/stm32/docs/figures/rt_device.png
