zengwangfa/Smart-Hive/new_node/bsp/stm32/docs/figures/run_flash.png

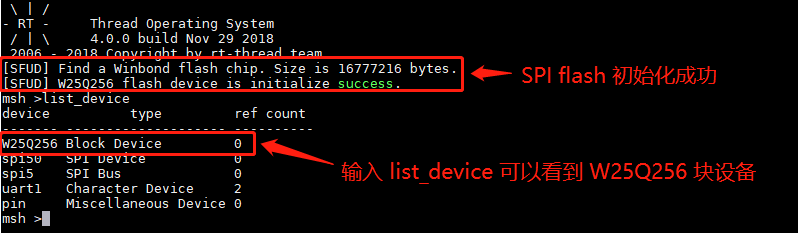
new_node/bsp/stm32/docs/figures/run_flash.png
