zengwangfa/Smart-Hive/new_node/bsp/stm32/docs/figures/save.png

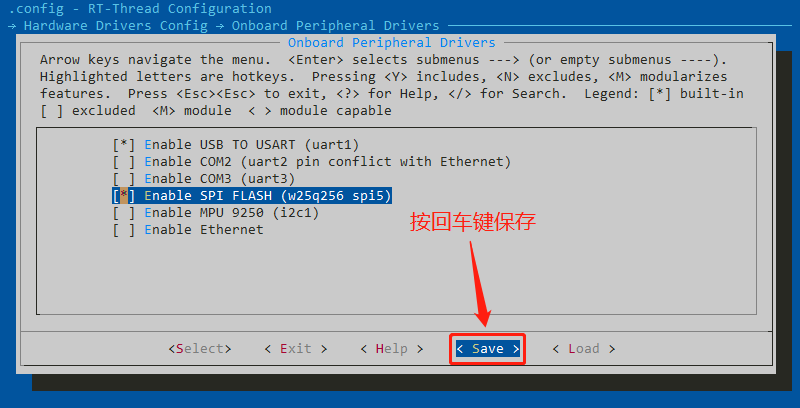
new_node/bsp/stm32/docs/figures/save.png
