zengwangfa/Smart-Hive/new_node/bsp/stm32/docs/figures/SConscript.png

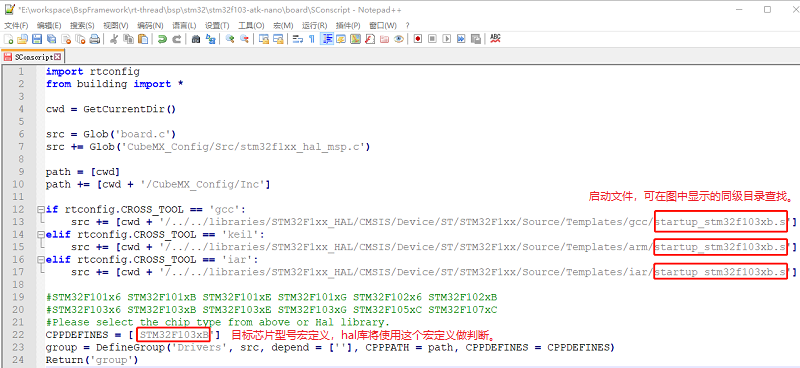
new_node/bsp/stm32/docs/figures/SConscript.png
