zengwangfa/Smart-Hive/new_node/bsp/stm32/docs/figures/spi_code.png

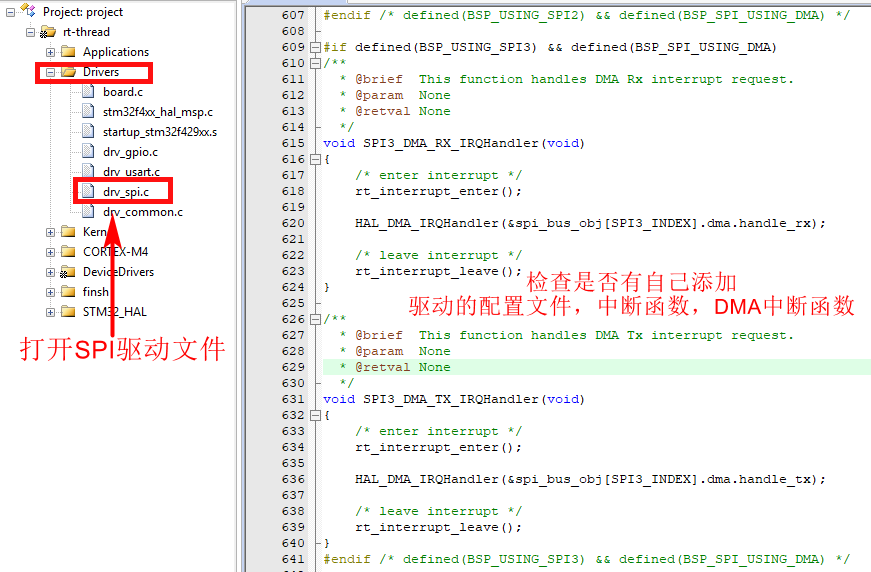
new_node/bsp/stm32/docs/figures/spi_code.png
