zengwangfa/Smart-Hive/new_node/bsp/stm32/docs/figures/spi_config.png

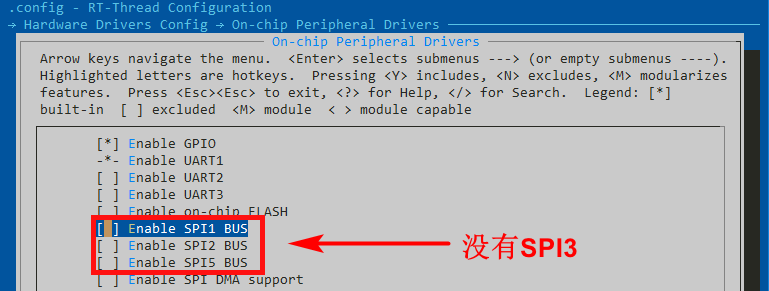
new_node/bsp/stm32/docs/figures/spi_config.png
