zengwangfa/Smart-Hive/new_node/bsp/stm32/docs/figures/spi_flash.png

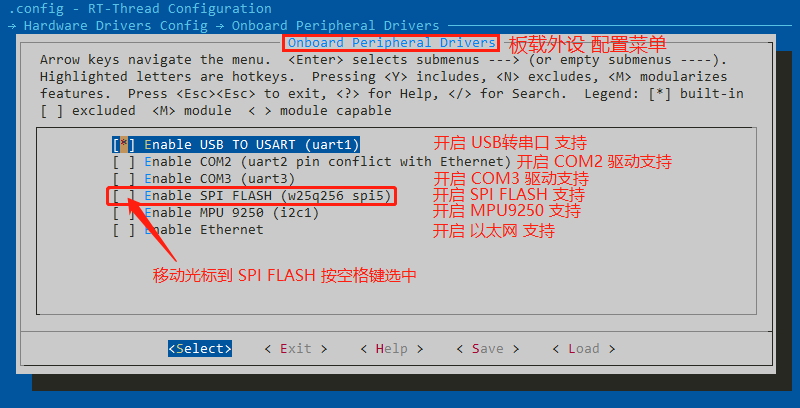
new_node/bsp/stm32/docs/figures/spi_flash.png
