zengwangfa/Smart-Hive/new_node/bsp/stm32/docs/figures/template_1.png

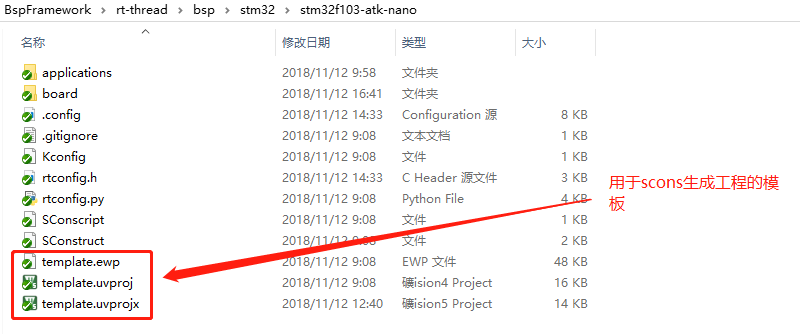
new_node/bsp/stm32/docs/figures/template_1.png
