zengwangfa/Smart-Hive/new_node/bsp/stm32/docs/figures/template_2.png

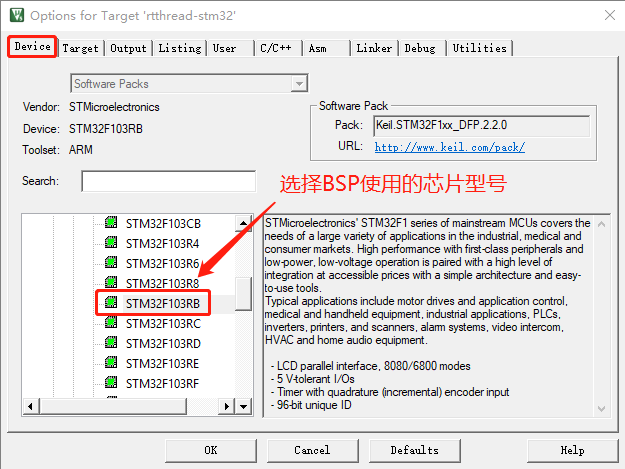
new_node/bsp/stm32/docs/figures/template_2.png
