zengwangfa/Smart-Hive/new_node/bsp/stm32/docs/figures/template_3.png

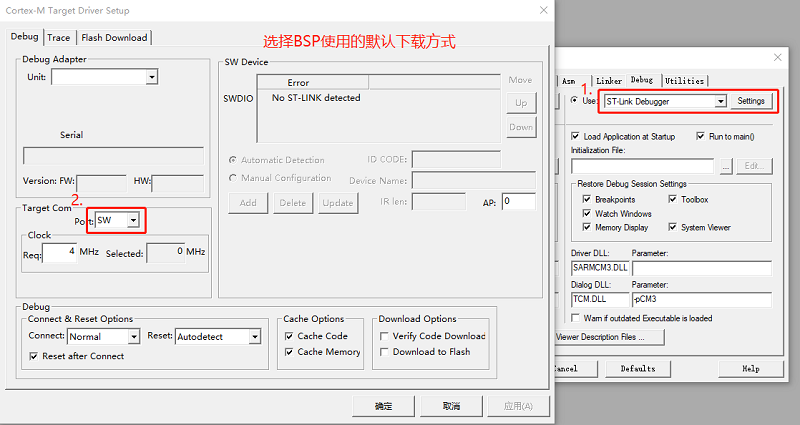
new_node/bsp/stm32/docs/figures/template_3.png
