zengwangfa/Smart-Hive/new_node/bsp/stm32/docs/figures/timer_config2.png

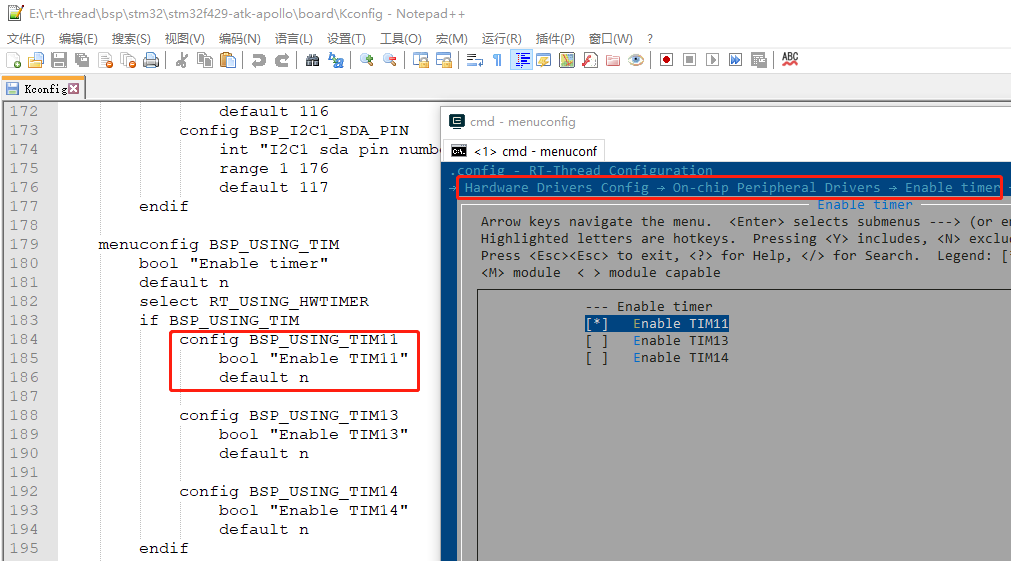
new_node/bsp/stm32/docs/figures/timer_config2.png
