zengwangfa/Smart-Hive/new_node/bsp/stm32/docs/figures/update.png

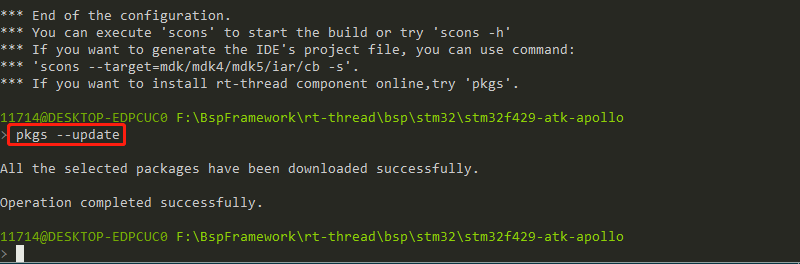
new_node/bsp/stm32/docs/figures/update.png
