zengwangfa/Smart-Hive/new_node/bsp/stm32/docs/figures/xCubeMX_1.png

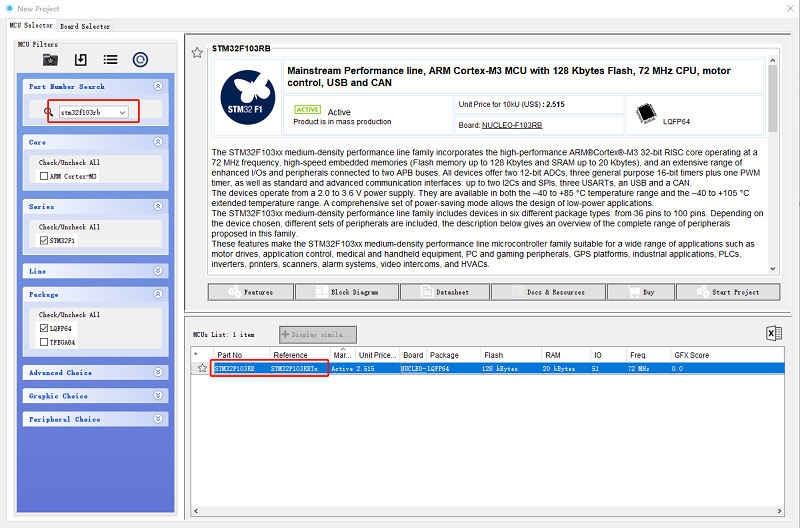
new_node/bsp/stm32/docs/figures/xCubeMX_1.png
