zengwangfa/Smart-Hive/new_node/bsp/stm32/stm32f405-smdz-breadfruit/figures/board.png

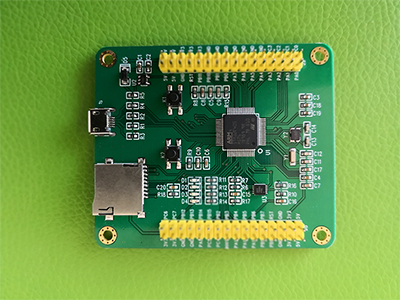
new_node/bsp/stm32/stm32f405-smdz-breadfruit/figures/board.png
