zengwangfa/Smart-Hive/new_node/documentation/doxygen/dfs.png

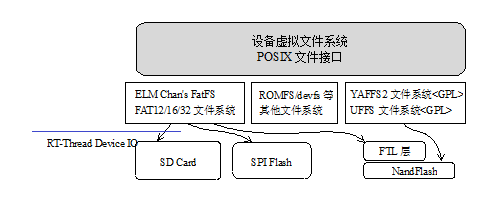
new_node/documentation/doxygen/dfs.png
