zengwangfa/Smart-Hive/new_node/documentation/doxygen/finsh.png

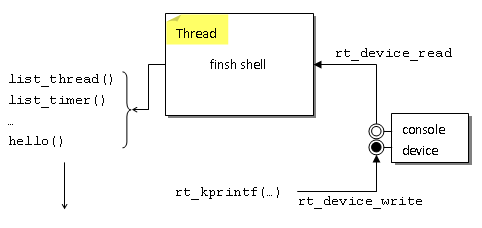
new_node/documentation/doxygen/finsh.png
