zengwangfa/Smart-Hive/new_node/documentation/doxygen/Kernel_Object.png

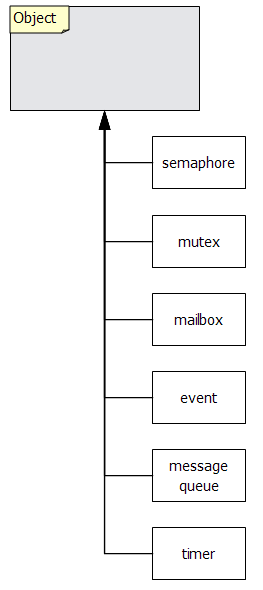
new_node/documentation/doxygen/Kernel_Object.png
