zengwangfa/Smart-Hive/new_node/documentation/doxygen/System_Arch.png

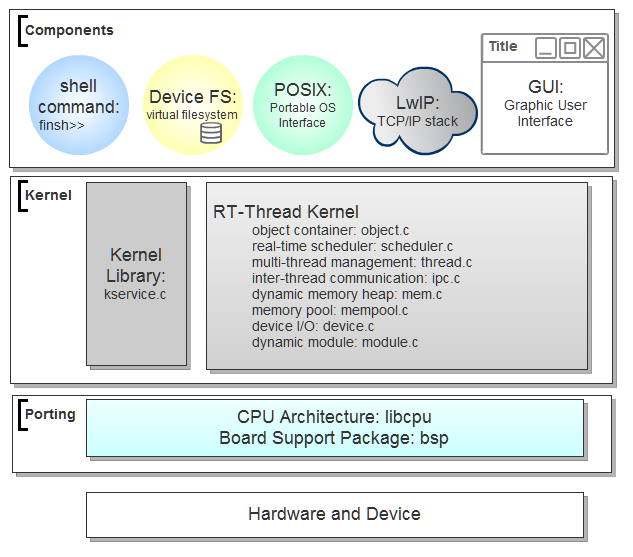
new_node/documentation/doxygen/System_Arch.png
