zengwangfa/Smart-Hive/new_node/documentation/doxygen/Thread_Scheduler.png

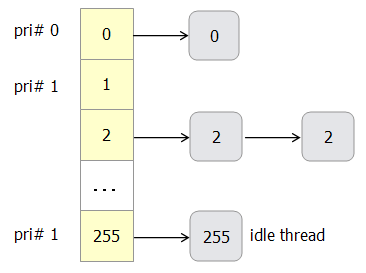
new_node/documentation/doxygen/Thread_Scheduler.png
