zengwangfa/Smart-Hive/new_node/components/dfs/filesystems/uffs/doc/uffs-serial-num-relationship.JPG

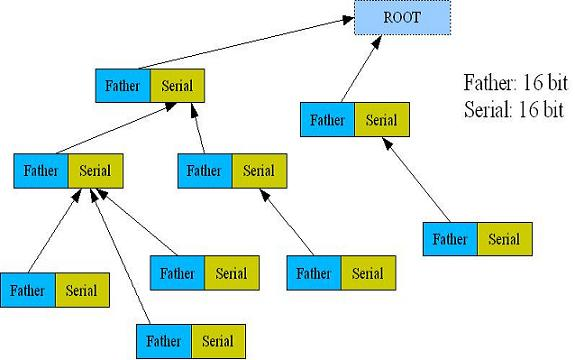
new_node/components/dfs/filesystems/uffs/doc/uffs-serial-num-relationship.JPG
