zengwangfa/Smart-Hive/software/node_PCB_test/figures/figure1.png

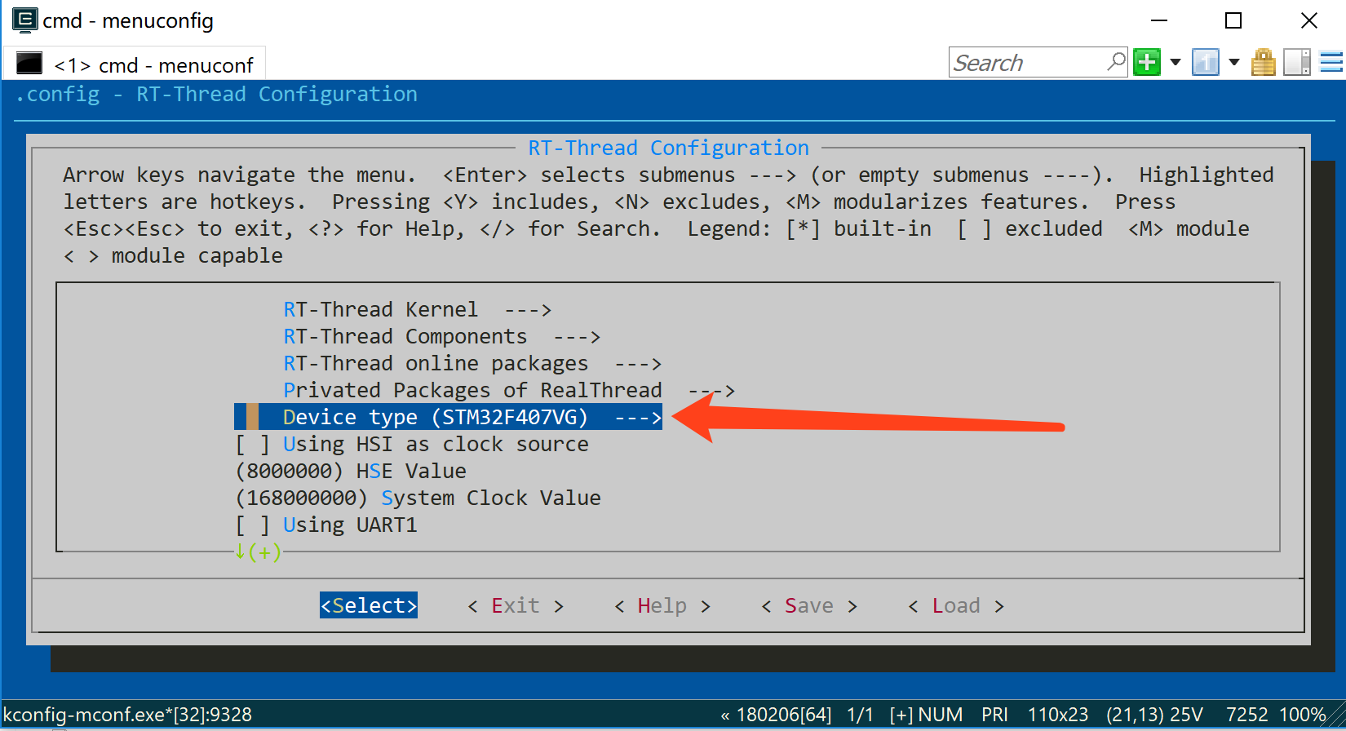
software/node_PCB_test/figures/figure1.png
