zengwangfa/Smart-Hive/software/node_PCB_test/figures/figure2.png

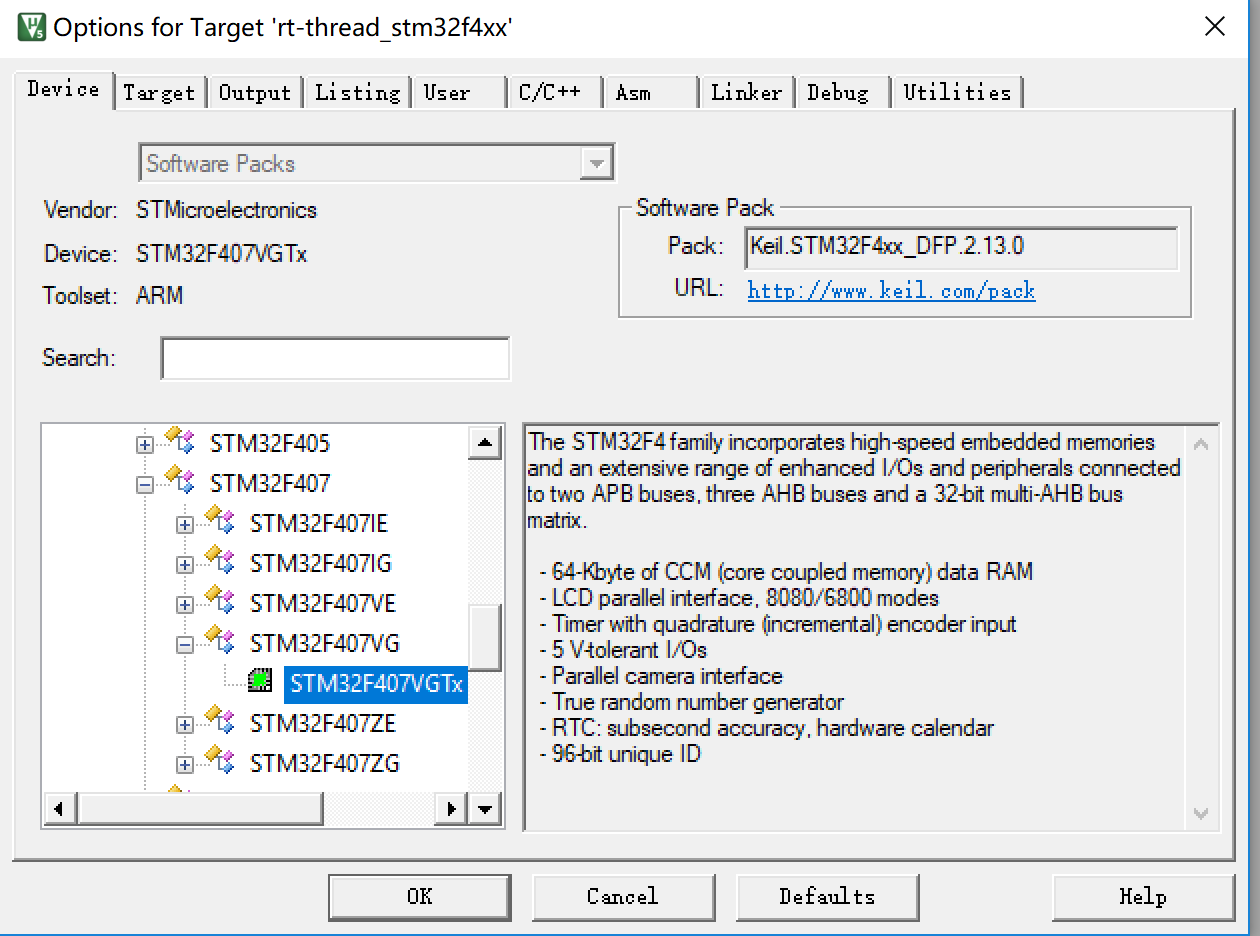
software/node_PCB_test/figures/figure2.png
