zengwangfa/Smart-Hive/new_node/bsp/stm32/stm32f405-smdz-breadfruit/board/radio/radio_trans_soft.c

/*
 * This file is part of the ART-6LoWPAN Radio Library.
 *
 * Copyright (c) 2017, Armink, <armink.ztl@gmail.com>
 * Copyright (c) 2017, xidongxu, <xi_dongxu@126.com>
 *
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
 * Function: Radio transition software process. It provide API to contiki radio driver layer.
 * Created on: 2017-09-15
 */

#include "radio_cfg.h"

//#define DRV_DEBUG
#define LOG_TAG             "radio_trans"
#include <drv_log.h>

#include "radio_hal.h"
#include <rthw.h>
#include <rtthread.h>
#include <rtdevice.h>
#include <stdio.h>
#include <string.h>
#include <stdbool.h>
#include <time.h>
#include "Si446x/si446x_api_lib.h"
#include "list.h"

/* 发送缓冲区大小 */
#ifndef RADIO_TRANS_TX_FIFO_SIZE
#define RADIO_TRANS_TX_FIFO_SIZE                 (2*1024)
#endif
/* 接收缓冲区大小 */
#ifndef RADIO_TRANS_RX_FIFO_SIZE
#define RADIO_TRANS_RX_FIFO_SIZE                 (2*1024)
#endif
/* 已接收报文数据链表的最大长度 */
#ifndef RADIO_TRANS_RX_PKGS_LIST_MAX_LEN
#define RADIO_TRANS_RX_PKGS_LIST_MAX_LEN         32
#endif
/* 射频数据传输的校验方式 ， 【注意】：经过验证 SI4463 的硬件 CRC 不可靠，所以本驱动使用软件完成 CRC 校验 */
#ifndef RADIO_TRANS_CRC_BIT
#define RADIO_TRANS_CRC_BIT                      16
#endif
/* 射频数据 filed1 默认不使用位翻转 */
#ifndef RADIO_FILED1_BIT_ORDER_REVERSE
#define RADIO_FILED1_BIT_ORDER_REVERSE           0
#endif
/* 发送数据超时 */
#ifndef RADIO_SEND_TIMEOUT
    #if RF_CORE_CONF_DATARATE_20K
        #define RADIO_SEND_TIMEOUT               (RT_TICK_PER_SECOND/5)
    #elif RF_CORE_CONF_DATARATE_10K
        #define RADIO_SEND_TIMEOUT               (RT_TICK_PER_SECOND/3)
    #elif RF_CORE_CONF_DATARATE_4800
        #define RADIO_SEND_TIMEOUT               (RT_TICK_PER_SECOND/2)
    #elif RF_CORE_CONF_DATARATE_2400
        #define RADIO_SEND_TIMEOUT               (RT_TICK_PER_SECOND/1)
    #endif /* RF_CORE_CONF_DATARATE_20K */
#endif /* RADIO_SEND_TIMEOUT */
/* 接收数据超时 */
#ifndef RADIO_RECV_TIMEOUT
    #if RF_CORE_CONF_DATARATE_20K
        #define RADIO_RECV_TIMEOUT               (RT_TICK_PER_SECOND/5)
    #elif RF_CORE_CONF_DATARATE_10K
        #define RADIO_RECV_TIMEOUT               (RT_TICK_PER_SECOND/3)
    #elif RF_CORE_CONF_DATARATE_4800
        #define RADIO_RECV_TIMEOUT               (RT_TICK_PER_SECOND/2)
    #elif RF_CORE_CONF_DATARATE_2400
        #define RADIO_RECV_TIMEOUT               (RT_TICK_PER_SECOND/1)
    #endif /* RF_CORE_CONF_DATARATE_20K */
#endif /* RADIO_RECV_TIMEOUT */
/* 最大报文长度（IEEE802.15.4 最大帧长度 127） */
#ifndef RADIO_PKT_MAX_LEN
#define RADIO_PKT_MAX_LEN                        127
#endif
/* 命令出错次数阈值，超过该次数，则对射频模块进行重新初始化 */
#define CMD_ERR_THRESHOLD_FOR_REINIT             5

/* 发送数据与接收数据事件 */
enum {
    RADIO_TX_FINISH    = (1L << 0), /* 发送完成 */
    RADIO_TX_TIMEOUT   = (1L << 1), /* 发送超时 */
    RADIO_RX_FINISH    = (1L << 2), /* 接收完成 */
    RADIO_RX_TIMEOUT   = (1L << 3), /* 接收超时 */
    RADIO_RX_CRC_ERR   = (1L << 4)  /* 接收出错 */
};

/* 802.15.4g 射频收发数据的基本单位：报文 */
struct radio_pkt {
    struct radio_pkt *next;
    int rssi;
    size_t len;
    uint8_t *data;
};
typedef struct radio_pkt *radio_pkt_t;

/* 传输统计信息 */
struct trans_stat {
    /* 传输成功报文数量 */
    size_t success_pkt_num;
    /* 传输失败报文数量 */
    size_t failed_pkt_num;
    /* 总计传输成功的数据量，单位：字节 */
    size_t total_byte;
};
typedef struct trans_stat *trans_stat_t;

/* 收发数据超时时间 单位：毫秒 */
#define TRANS_TIMEOUT               (10*1000)

/* SI446x packet header length for 802.15.4g mode */
#define SI446X_PHR_LENGTH            2
/* CRC 校验数据长度，单位：字节 */
#if RADIO_TRANS_CRC_BIT == 16
#define SI446X_CRC_LENGTH            2
#elif RADIO_TRANS_CRC_BIT == 32
#define SI446X_CRC_LENGTH            4
#endif /* RADIO_TRANS_CRC_BIT == 16 */

/* 传输数据锁 */
static rt_mutex_t trans_locker = NULL;
/* 中断通知事件 */
static rt_sem_t isr_notice = NULL;
/* 接收完成通知事件 */
static rt_event_t radio_event = NULL;
/* si446x 发送 FIFO 上次发送的数据大小 */
static size_t si446x_tx_fifo_last_size = 0;
/* 发送 FIFO 及 si446x FIFO 中剩余的，等待通过射频发送的数据大小 */
static size_t tx_reamin_size = 0;
/* 此次传输总计需要发送的数据大小 */
static size_t tx_total_size = 0;
/* 接收数据报文中 payload 的长度 */
static size_t rx_payload_length = 0;
/* 接收数据报文中 filed2 的长度 */
static size_t rx_filed2_length = 0;
/* 接收缓冲区中已经接收到的数据大小 */
static size_t rx_buf_recived_size = 0;
/* 发送数据缓冲区 */
static struct rt_ringbuffer tx_fifo = { 0 };
/* 接收数据缓冲区 */
static struct rt_ringbuffer rx_fifo = { 0 };
/* 存放已接收到报文数据的链表 @see radio_pkt_t */
LIST(rx_pkts);
/* 当前是否正在发送数据 */
static bool is_sending = false;
/* 当前是否正在接收数据 */
static bool is_recving = false;
/* 射频中断信号处理线程 */
static rt_thread_t radio_isr = NULL;
/* 等待接收完成事件的协程 */
struct process *wait_recved_process = NULL;
/* 开始接收时间、开始发送时间 */
static time_t recv_start, send_start;
/* 接收超时控制定时器 */
static rt_timer_t recv_timer;
/* 发送超时控制定时器 */
static rt_timer_t send_timer;
/* 接收完成钩子函数 */
static void (*recved_hook)(size_t recv_len);
/* 收发统计信息 */
static struct trans_stat send_stat = { 0 }, recv_stat = { 0 };
/* 命令出错计数 */
static size_t cmd_err_count = 0;

extern const tRadioConfiguration *pRadioConfiguration;
extern void si446x_pa_enabled(bool enabled);
extern void si446x_trans_led_ctrl(bool rx_on, bool tx_on);
static void radio_isr_entry(void* parameter);
static uint16_t calc_crc16(const char *data, size_t size);

#if RADIO_FILED1_BIT_ORDER_REVERSE
static uint8_t bit_order_reverse(uint8_t byte_to_reverse) {
    byte_to_reverse = (byte_to_reverse & 0xF0) >> 4 | (byte_to_reverse & 0x0F) << 4;
    byte_to_reverse = (byte_to_reverse & 0xCC) >> 2 | (byte_to_reverse & 0x33) << 2;
    byte_to_reverse = (byte_to_reverse & 0xAA) >> 1 | (byte_to_reverse & 0x55) << 1;
    return byte_to_reverse;
}
#endif

static uint16_t get_payload_length_from_phr(uint8_t* phr) {
    uint16_t len = (phr[0] & 0x03) * 256 + phr[1] - SI446X_CRC_LENGTH;

    return len > RADIO_PKT_MAX_LEN ? RADIO_PKT_MAX_LEN : len;
}

static void set_field1(char *field1, bool dw, uint16_t field2_len) {
    field1[0] = 0;
    field1[1] = 0;
    /* 加上 crc 的长度 */
    field2_len += SI446X_CRC_LENGTH;
#if RADIO_FILED1_BIT_ORDER_REVERSE
    field1[0] |= bit_order_reverse(field2_len >> 8);
#else
    field1[0] |= field2_len >> 8;
#endif /* RADIO_FILED1_BIT_ORDER_REVERSE */

#if RADIO_IEEE_802_15_4_PACKET
#if RADIO_TRANS_CRC_BIT == 16
    /* CRC16 */
    field1[0] |= 0x08;
#elif RADIO_TRANS_CRC_BIT == 32
    /* CRC32 */
    field1[0] |= 0x00;
#endif /* RADIO_TRANS_CRC_BIT == 16 */
    if (dw) {
        field1[0] |= 0x10;
    }
#endif /* RADIO_IEEE_802_15_4_PACKET */

#if RADIO_FILED1_BIT_ORDER_REVERSE
    field1[1] = bit_order_reverse(field2_len);
#else
    field1[1] = field2_len;
#endif /* RADIO_FILED1_BIT_ORDER_REVERSE */
}

static void trans_fifo_clear(struct rt_ringbuffer *fifo) {
    rt_ringbuffer_reset(fifo);
}

static void print_hex(const uint8_t *packet, size_t size, uint8_t log_lvl) 
{
    size_t i;
    char *hex;

    RT_ASSERT(packet);

    if (!size)
    {
        return;
    }

    hex = rt_malloc(size * 5 + 1);
    if (hex)
    {
        for (i = 0; i < size; i++)
        {
            snprintf(hex + 5 * i, 6, " 0x%02X", *(packet + i));
        }
        
        switch (log_lvl) 
        {
            case DBG_ERROR:
                LOG_E("package: %s", hex + 1);
                break;
            case DBG_WARNING:
                LOG_W("package: %s", hex + 1);
                break;
            case DBG_INFO:
                LOG_I("package: %s", hex + 1);
                break;
            case DBG_LOG:
                LOG_D("package: %s", hex + 1);
                break;
        }
        rt_free(hex);
    } 
    else 
    {
        LOG_W("not enough memory!");
    }
}

/**
 * 从硬件 FIFO 中取出接收的数据
 *
 * @param recv_is_finish 接收是否完成
 *
 * @return 接收到并且拷贝完成的数据
 */
static size_t recv_from_hw_fifo(bool recv_is_finish) {
    static uint8_t buffer[SI466X_FIFO_SIZE] = { 0 };
    size_t copy_size = 0;
    uint8_t phr[SI446X_PHR_LENGTH], hw_fifo_count = 0;
    static bool phr_is_detected = false;

    /* 获取 SI446X 硬件 FIFO 信息 */
    radio_cmd_reply_lock();
    si446x_fifo_info(0);
    hw_fifo_count = Si446xCmd.FIFO_INFO.RX_FIFO_COUNT;
    radio_cmd_reply_unlock();

    if (hw_fifo_count > SI466X_FIFO_SIZE) {
        hw_fifo_count = SI466X_FIFO_SIZE;
        LOG_W("radio hardware FIFO size has some error.");
    }
    /* 是否已经检测到过 PHR */
    if (!phr_is_detected) {
        /* 清理之前可能残留的已接收数据 */
        trans_fifo_clear(&rx_fifo);
        if (hw_fifo_count >= sizeof(phr)) {
            phr_is_detected = true;
            /* 取出 PHR */
            si446x_read_rx_fifo(sizeof(phr), phr);
            /* 计算 payload length */
            rx_payload_length = get_payload_length_from_phr(phr);
            /* 计算 filed2 length */
            rx_filed2_length = rx_payload_length + SI446X_CRC_LENGTH;
            if (sizeof(phr) + rx_filed2_length <= hw_fifo_count) {
                copy_size = rx_filed2_length;
            } else {
                copy_size = hw_fifo_count - sizeof(phr);
            }
            LOG_I("get PHR([0]:0x%02X, [1]:0x%02X) payload length is %d bytes", phr[0], phr[1], rx_payload_length);
        }
    } else {
        copy_size = hw_fifo_count;
        if ((rx_buf_recived_size + copy_size) >= rx_filed2_length) {
            copy_size = rx_filed2_length - rx_buf_recived_size;
        }
    }
    if (copy_size) {
        /* 从硬件 FIFO 中取出数据 */
        si446x_read_rx_fifo(copy_size, buffer);
        /* 打印接收到的数据 */
        print_hex(buffer, copy_size, DBG_INFO);
        rx_buf_recived_size += copy_size;
        /* 数据放置软件 FIFO 中 */
        rt_ringbuffer_put_force(&rx_fifo, (rt_uint8_t *) buffer, copy_size);
    }
    /* 接收完成，还原状态 */
    if (recv_is_finish) {
        phr_is_detected = false;
    }

    return copy_size;
}

static void trans_lock(void) {
    rt_mutex_take(trans_locker, RT_WAITING_FOREVER);
}

static void trans_unlock(void) {
    rt_mutex_release(trans_locker);
}

static void transmit_timeout(void *ptr) {
    trans_lock();
    if (is_sending) {
        LOG_W("radio send timeout.");
        send_stat.failed_pkt_num ++;
        /* 关闭射频模块PA */
        si446x_pa_enabled(false);
        /* 启动接收 */
        radio_start_rx(pRadioConfiguration->Radio_ChannelNumber, 0u);
        is_sending = false;
        rt_event_send(radio_event, RADIO_TX_TIMEOUT);
    } else {
        LOG_W("radio receive timeout.");
        /* Reset FIFO */
        si446x_fifo_info(SI446X_CMD_FIFO_INFO_ARG_FIFO_RX_BIT);
        rx_buf_recived_size = 0;
        rx_payload_length = 0;
        recv_stat.failed_pkt_num ++;
        /* 启动接收 */
        radio_start_rx(pRadioConfiguration->Radio_ChannelNumber, 0u);
        is_recving = false;
        rt_event_send(radio_event, RADIO_RX_TIMEOUT);
    }
    si446x_trans_led_ctrl(false, false);
    trans_unlock();
}

#if RAW_RADIO_TEST
static void radio_test_entry(void* parameter) {
    extern bool si446x_test_key_press(void);
    extern rt_err_t radio_pkt_send_sync(const uint8_t *buf, size_t size);
    uint8_t radio_data[] = "Hello ART-6LoWPAN!";

    while (true) {
        if (si446x_test_key_press()) {
            /* 发送 18+1 字节数据 */
            radio_pkt_send_sync(radio_data, sizeof(radio_data));
        }
        /* 10ms 间隔 */
        rt_thread_delay(rt_tick_from_millisecond(10));
    }
}
#endif /* RAW_RADIO_TEST */

/**
 * 射频传输软件处理部分初始化
 */
void radio_transmit_software_init(void) {
    static bool init_ok = false;

    if (init_ok) {
        return;
    }
    /* 传输数据锁 */
    trans_locker = rt_mutex_create("trans_lock", RT_IPC_FLAG_FIFO);
    /* 创建必须成功，否则断言提示开发者 */
    RT_ASSERT(trans_locker);

    /* 初始化发送数据缓冲区 */
    rt_uint8_t * tx_buf = (rt_uint8_t *) rt_malloc(RADIO_TRANS_TX_FIFO_SIZE * sizeof(rt_uint8_t));
    /* 创建必须成功，否则断言提示开发者 */
    RT_ASSERT(tx_buf);
    rt_ringbuffer_init(&tx_fifo, tx_buf, RADIO_TRANS_TX_FIFO_SIZE);

    /* 初始化接收数据缓冲区 */
    rt_uint8_t * rx_buf = (rt_uint8_t *) rt_malloc(RADIO_TRANS_RX_FIFO_SIZE * sizeof(rt_uint8_t));
    /* 创建必须成功，否则断言提示开发者 */
    RT_ASSERT(rx_buf);
    rt_ringbuffer_init(&rx_fifo, rx_buf, RADIO_TRANS_RX_FIFO_SIZE);

    /* 初始化报文数据的链表 */
    list_init(rx_pkts);

    isr_notice = rt_sem_create("radio_isr", 0, RT_IPC_FLAG_FIFO);
    /* 创建必须成功，否则断言提示开发者 */
    RT_ASSERT(isr_notice);

    radio_event = rt_event_create("radio", RT_IPC_FLAG_FIFO);
    /* 创建必须成功，否则断言提示开发者 */
    RT_ASSERT(radio_event);

    recv_timer = rt_timer_create("radio_recv", transmit_timeout, NULL, RADIO_RECV_TIMEOUT,
            RT_TIMER_FLAG_ONE_SHOT | RT_TIMER_FLAG_SOFT_TIMER);
    /* 创建必须成功，否则断言提示开发者 */
    RT_ASSERT(recv_timer);

    send_timer = rt_timer_create("radio_send", transmit_timeout, NULL, RADIO_RECV_TIMEOUT,
            RT_TIMER_FLAG_ONE_SHOT | RT_TIMER_FLAG_SOFT_TIMER);
    /* 创建必须成功，否则断言提示开发者 */
    RT_ASSERT(send_timer);

    /* 初始化中断处理线程 */
    radio_isr = rt_thread_create("radio_isr", radio_isr_entry, NULL, 2048, 3, 20);
    /* 创建必须成功，否则断言提示开发者 */
    RT_ASSERT(radio_isr);
    rt_thread_startup(radio_isr);

#if RAW_RADIO_TEST
    /* 初始化射频测试线程 */
    rt_thread_t radio_test_thread = rt_thread_create("radio_test", radio_test_entry, NULL, 1024, 15, 50);
    if (radio_test_thread) {
        rt_thread_startup(radio_test_thread);
    }
#endif /* RAW_RADIO_TEST */

    init_ok = true;
}

/**
 * 通知已产生射频中断
 */
void radio_notice_irq(void) {
    if (isr_notice) {
        rt_sem_release(isr_notice);
    }
}

bool radio_is_sending(void) {
    return is_sending;
}

bool radio_is_recving(void) {
    return is_recving;
}

/**
 * 射频数据报文发送，以 802.15.4g 报文为单位。@note 此方法为非阻塞方法
 *
 * @param buf 发送报文缓冲区
 * @param size 该报文数据的大小
 *
 * @return 结果 RT_EOK: 成功，-RT_EBUSY：当前正在发送数据，请稍后
 */
rt_err_t radio_pkt_send(const uint8_t *buf, size_t size) {
    static uint8_t buffer[SI466X_FIFO_SIZE] = { 0 };
    char field1[SI446X_PHR_LENGTH] = { 0 };
    uint32_t crc = 0;
    rt_uint8_t field2_crc[SI446X_CRC_LENGTH] = { 0 };
    uint8_t filed2_size_high, filed2_size_low;
    rt_size_t filed2_len;
    rt_tick_t timeout = RADIO_SEND_TIMEOUT;
    rt_err_t result = RT_EOK;

    RT_ASSERT(buf);

    trans_lock();

    if (size > RADIO_PKT_MAX_LEN) {
        LOG_W("send size must <= %d", RADIO_PKT_MAX_LEN);
        result = -RT_ERROR;
        goto __exit;
    }

    if (is_sending) {
        LOG_W("radio is sending, please wait and retry.");
        result = -RT_EBUSY;
        goto __exit;
    }
    is_sending = true;

    /* 清空发送软件 FIFO */
    trans_fifo_clear(&tx_fifo);
    /* 计算 filed1 */
    set_field1(field1, true, size);
    /* 将 field1 及 filed2 分别放入软件发送 FIFO */
    rt_ringbuffer_put_force(&tx_fifo, (rt_uint8_t *) field1, sizeof(field1));
    rt_ringbuffer_put_force(&tx_fifo, (rt_uint8_t *) buf, size);

    /* 计算并设置CRC */
#if RADIO_TRANS_CRC_BIT == 16
    crc = calc_crc16((const char *) buf, size);
    field2_crc[0] = crc >> 8;
    field2_crc[1] = crc & 0xFF;
#elif RADIO_TRANS_CRC_BIT == 32
    #error "not supported!"
#endif
    /* 将 filed2_crc 放入软件发送 FIFO */
    rt_ringbuffer_put_force(&tx_fifo, field2_crc, sizeof(field2_crc));

    /* 重新计算待发送数据长度 */
    size += SI446X_PHR_LENGTH + SI446X_CRC_LENGTH;
    tx_reamin_size = size;
    tx_total_size = size;

    if (size > SI466X_FIFO_SIZE) {
        si446x_tx_fifo_last_size = SI466X_FIFO_SIZE;
    } else {
        si446x_tx_fifo_last_size = size;
    }

    LOG_I("send data %d byte, PHR[0]:0x%02X, PHR[1]:0x%02X, CRC:0x%08X,", size, field1[0], field1[1], crc);
    /* 打印 filed2 中的 payload */
    print_hex(buf, size - SI446X_PHR_LENGTH - SI446X_CRC_LENGTH, DBG_INFO);

    send_start = clock();
    si446x_trans_led_ctrl(false, true);

    /* 清空发送硬件 FIFO */
    si446x_fifo_info(SI446X_CMD_FIFO_INFO_ARG_FIFO_TX_BIT);

    /* pkt 总长度减去 filed1 的长度*/
    filed2_len = rt_ringbuffer_data_len(&tx_fifo) - RADIO_PH_FILE1_LEN;
    filed2_size_high = filed2_len >> 8;
    filed2_size_low = filed2_len;
    /* 配置 field2 长度 */
    si446x_set_property(SI446X_PROP_GRP_ID_PKT, 2, SI446X_PROP_PKT_FIELD_2_LENGTH_FIELD_2_LENGTH_12_8_INDEX,
            filed2_size_high, filed2_size_low);
    /* 取出第一次可发送的数据 */
    rt_ringbuffer_get(&tx_fifo, (rt_uint8_t *) buffer, si446x_tx_fifo_last_size);
    /* 打开射频模块PA */
    si446x_pa_enabled(true);
    /* 启动发送 */
    radio_start_tx_variable_packet_multifield(pRadioConfiguration->Radio_ChannelNumber, buffer,
            si446x_tx_fifo_last_size);
    /* 启动传输超时定时器 */
    rt_timer_control(send_timer, RT_TIMER_CTRL_SET_TIME, (void *) &timeout);
    rt_timer_start(send_timer);

__exit:
    trans_unlock();

    return result;
}

/**
 * 射频数据报文采用同步方式发送，以 802.15.4g 报文为单位。@note 此方法为阻塞方法
 *
 * @param buf 发送报文缓冲区
 * @param size 该报文数据的大小
 *
 * @return 结果 RT_EOK: 成功，-RT_EBUSY：当前正在发送数据，请稍后，-RT_ETIMEOUT 发送数据超时
 */
rt_err_t radio_pkt_send_sync(const uint8_t *buf, size_t size) {
    rt_err_t result = RT_EOK;
    rt_uint32_t recved;

    if ((result = radio_pkt_send(buf, size)) == RT_EOK) {
        /* 清空已存在事件 */
        rt_event_control(radio_event, RT_IPC_CMD_RESET, NULL);
        if (rt_event_recv(radio_event, RADIO_TX_FINISH | RADIO_TX_TIMEOUT, RT_EVENT_FLAG_CLEAR | RT_EVENT_FLAG_OR,
                RT_WAITING_FOREVER, &recved) == RT_EOK) {
            if (recved & RADIO_TX_TIMEOUT) {
                result = -RT_ETIMEOUT;
            }
            if (recved & RADIO_TX_FINISH) {
                result = RT_EOK;
            }
        } else {
            result = -RT_ETIMEOUT;
        }
    }

    return result;
}

/**
 * 设置接收完成钩子函数
 *
 * @param hook 钩子函数，将会在接收完成时执行
 */
void radio_recved_set_hook(void (*hook)(size_t recv_len)) {
    recved_hook = hook;
}

/**
 * 是否已接收到数据
 */
bool radio_has_recved_pkt(void) {
    bool has_pkt = false;

    trans_lock();
    if (list_length(rx_pkts)) {
        has_pkt = true;
    }
    trans_unlock();

    return has_pkt;
}

/**
 * 射频数据报文接收，以 802.15.4g 报文为单位。@note 此方法为非阻塞方法
 *
 * @param buf 接收报文缓冲区
 * @param size 缓冲区的大小
 * @param len 该报文数据的长度
 * @param rssi 接收该报文数据时的信号强度，单位 dbm
 *
 * @return 结果 RT_EOK: 成功，-RT_ERROR：没有数据
 */
rt_err_t radio_pkt_get_recved(uint8_t* buf, size_t size, size_t *len, int *rssi) {
    rt_err_t result = RT_EOK;

    RT_ASSERT(buf);
    RT_ASSERT(len);
    trans_lock();
    if (list_length(rx_pkts)) {
        radio_pkt_t pkt = list_pop(rx_pkts);
        if (pkt) {
            if (pkt->len > size) {
                *len = size;
            } else {
                *len = pkt->len;
            }
            memcpy(buf, pkt->data, *len);
            rt_free(pkt);
            *rssi = pkt->rssi;
        }
    } else {
        result = -RT_ERROR;
    }
    trans_unlock();

    return result;
}

/**
 * 接收数据完成的处理函数
 */
static void radio_recive_finished(int rssi) {
    uint32_t crc = 0, crc_recv = 0;
    bool has_crc_error = false;

    /* 重新启动接收 */
    radio_start_rx(pRadioConfiguration->Radio_ChannelNumber, 0u);
    si446x_trans_led_ctrl(false, false);
    LOG_D("RADIO_RX_FINISH: cost %3ld ms, total size %3d, rssi: %3ddBm, payload is %3d bytes", clock() - recv_start,
            SI446X_PHR_LENGTH + rx_filed2_length, rssi, rx_payload_length);
    /* 将接收到的报文数据，放置报文链表中 */
    if (list_length(rx_pkts) < RADIO_TRANS_RX_PKGS_LIST_MAX_LEN) {
        radio_pkt_t pkt = (radio_pkt_t)rt_malloc(RT_ALIGN(sizeof(struct radio_pkt), sizeof(size_t)) + rx_payload_length);
        if (pkt) {
            pkt->data = (uint8_t *) pkt + RT_ALIGN(sizeof(struct radio_pkt), sizeof(size_t));
            pkt->len = rx_payload_length;
            pkt->rssi = rssi;
            rt_ringbuffer_get(&rx_fifo, pkt->data, rx_payload_length);
            /* 重组接收到的 CRC 数据 */
            for (uint8_t i = 0, temp = 0; i < SI446X_CRC_LENGTH; i++) {
                rt_ringbuffer_getchar(&rx_fifo, &temp);
                crc_recv <<= 8;
                crc_recv |= temp;
            }
            /* 计算 CRC */
#if RADIO_TRANS_CRC_BIT == 16
            crc = calc_crc16((const char *) pkt->data, rx_payload_length);
#elif RADIO_TRANS_CRC_BIT == 32
            #error "not supported!"
#endif

            if (crc == crc_recv) {
                /* 添加到已接收到报文数据链表 */
                list_add(rx_pkts, pkt);
                recv_stat.success_pkt_num ++;
                recv_stat.total_byte += pkt->len;
            } else {
                LOG_W("CRC ERROR!");
                recv_stat.failed_pkt_num ++;
                /* 释放内存 */
                rt_free(pkt);
            }
        } else {
            LOG_W("Warning: No memory!");
        }
    } else {
        LOG_W("received package list is full.");
    }
    /* 停止接收定时器 */
    rt_timer_stop(recv_timer);
    rx_buf_recived_size = 0;
    rx_payload_length = 0;
    is_recving = false;
    if (recved_hook) {
        recved_hook(rx_payload_length);
    }
    /* 通知接收线程 */
    if (!has_crc_error) {
        rt_event_send(radio_event, RADIO_RX_FINISH);
    } else {
        rt_event_send(radio_event, RADIO_RX_CRC_ERR);
    }
}

/**
 * 射频中断信号处理线程
 */
static void radio_isr_entry(void* parameter) {
    static uint8_t buffer[SI466X_FIFO_SIZE] = { 0 };
    static size_t get_size = 0;
    static size_t copy_size = 0;
    static size_t last_tansed_size = 0;
    static uint8_t hw_fifo_space;
    static int latch_rssi;
    static uint8_t ph_int, modem_int, chip_int;

    while (true) {
        rt_sem_take(isr_notice, RT_WAITING_FOREVER);
        trans_lock();

        radio_cmd_reply_lock();
        /* 读取中断状态 */
        si446x_get_int_status(0, 0, 0);
        ph_int = Si446xCmd.GET_INT_STATUS.PH_PEND;
        modem_int = Si446xCmd.GET_INT_STATUS.MODEM_PEND;
        chip_int = Si446xCmd.GET_INT_STATUS.CHIP_PEND;
        radio_cmd_reply_unlock();

        /* 查看中断挂起状态信息 */
        LOG_I("irq pend int: 0x%02X, ph: 0x%02X, modem: 0x%02X, chip: 0x%02X", Si446xCmd.GET_INT_STATUS.INT_PEND, ph_int, modem_int, chip_int);
        /* 检测到同步码 */
        if (modem_int & SI446X_CMD_GET_INT_STATUS_REP_MODEM_PEND_SYNC_DETECT_PEND_BIT) {
            is_recving = true;
            recv_start = clock();
            si446x_trans_led_ctrl(true, false);
            /* 启动接收超时定时器 */
            rt_tick_t timeout = RADIO_RECV_TIMEOUT;
            rt_timer_control(recv_timer, RT_TIMER_CTRL_SET_TIME, (void *) &timeout);
            rt_timer_start(recv_timer);
            latch_rssi = radio_get_latch_rssi();
        }
        /* 发送完成中断产生 */
        if (ph_int & SI446X_CMD_GET_INT_STATUS_REP_PH_PEND_PACKET_SENT_PEND_BIT) {
            if (tx_reamin_size <= si446x_tx_fifo_last_size) {
                tx_reamin_size = 0;
            } else {
                tx_reamin_size -= si446x_tx_fifo_last_size;
                LOG_W("remain %d bytes not send", tx_reamin_size);
            }
            /* 停止发送定时器 */
            rt_timer_stop(send_timer);
            send_stat.success_pkt_num ++;
            send_stat.total_byte += tx_total_size - SI446X_PHR_LENGTH - SI446X_CRC_LENGTH;
            si446x_trans_led_ctrl(false, false);
            LOG_D("RADIO_TX_FINISH: cost %3ld ms, total size %3d", clock() - send_start, tx_total_size);
            /* 关闭射频模块PA */
            si446x_pa_enabled(false);
            /* 启动接收 */
            radio_start_rx(pRadioConfiguration->Radio_ChannelNumber, 0u);
            is_sending = false;
            rt_event_send(radio_event, RADIO_TX_FINISH);
            /* 发送缓冲区几乎空中断产生 */
        } else if ((ph_int & SI446X_CMD_GET_INT_STATUS_REP_PH_PEND_TX_FIFO_ALMOST_EMPTY_PEND_BIT) && is_sending) {
            /* 获取 SI446X 硬件 FIFO 信息 */
            radio_cmd_reply_lock();
            si446x_fifo_info(0);
            hw_fifo_space = Si446xCmd.FIFO_INFO.TX_FIFO_SPACE;
            radio_cmd_reply_unlock();

            if (hw_fifo_space > SI466X_FIFO_SIZE) {
                hw_fifo_space = SI466X_FIFO_SIZE;
                LOG_W("radio hardware FIFO size has some error.");
            }
            /* 计算上次已传输（发送）的数据长度 */
            if (si446x_tx_fifo_last_size >= SI466X_FIFO_SIZE - hw_fifo_space) {
                last_tansed_size = si446x_tx_fifo_last_size - (SI466X_FIFO_SIZE - hw_fifo_space);
            } else {
                LOG_E("si446x_tx_fifo_last_size(%d) or hw_fifo_count(%d) has some error.", si446x_tx_fifo_last_size,
                        hw_fifo_space);
                last_tansed_size = 0;
            }
            /* 重新计算剩余需要经过射频发送的数据 */
            if (tx_reamin_size >= last_tansed_size) {
                tx_reamin_size -= last_tansed_size;
            } else {
                LOG_E("tx_reamin_size(%d) or last_tansed_size(%d) has some error.", tx_reamin_size, last_tansed_size);
                tx_reamin_size = 0;
            }
            /* 计算软件 FIFO 中存放的数据长度 */
            copy_size = rt_ringbuffer_data_len(&tx_fifo);
            /* 对比剩余需要放入硬件 FIFO 中的数据长度，是否大于 si446x FIFO 的剩余空间 */
            if (copy_size > hw_fifo_space) {
                /* si446x 发送 FIFO 被全部填充满 */
                copy_size = hw_fifo_space;
                si446x_tx_fifo_last_size = SI466X_FIFO_SIZE;
            } else {
                /* 将剩余软件发送 FIFO 中未发送的全部拷贝过来 */
                si446x_tx_fifo_last_size = (SI466X_FIFO_SIZE - hw_fifo_space) + copy_size;
            }
            /* 从 软件 发送 FIFO 中取出待发送的数据 */
            get_size = rt_ringbuffer_get(&tx_fifo, (rt_uint8_t *) buffer, copy_size);
            if (get_size != copy_size) {
                LOG_E("software FIFO has some error, copy_size(%d) != get_size(%d)", copy_size, get_size);
            }
            if (get_size) {
                /* 发送数据 */
                si446x_write_tx_fifo(get_size, buffer);
            }
            LOG_I("RADIO_TX_ALMOST_EMPTY: last packet sent %d bytes, add %d bytes to FIFO, remain size %d bytes",
                    last_tansed_size, get_size, tx_reamin_size);
            /* 接收完成中断产生 */
        } else if (ph_int & SI446X_CMD_GET_INT_STATUS_REP_PH_PEND_PACKET_RX_PEND_BIT) {
            /* 从硬件 FIFO 中取出接收的数据 */
            copy_size = recv_from_hw_fifo(true);
            /* 接收完成处理 */
            radio_recive_finished(latch_rssi);
            /* 接收缓冲区几乎满中断产生 */
        } else if (ph_int & SI446X_CMD_GET_INT_STATUS_REP_PH_PEND_RX_FIFO_ALMOST_FULL_PEND_BIT) {
            /* 从硬件 FIFO 中取出接收的数据 */
            copy_size = recv_from_hw_fifo(false);
            LOG_I("RADIO_RX_ALMOST_FULL: current packet received %d bytes, total size %d bytes", copy_size,
                    rx_buf_recived_size);
            /* 超过 filed2 长度则认为接收完成，强制停止数据接收 */
            if (rx_buf_recived_size >= rx_filed2_length) {
                recv_from_hw_fifo(true);
                /* 接收完成处理 */
                radio_recive_finished(latch_rssi);
            }
        }
        /* 命令出错 */
        if (chip_int & SI446X_CMD_GET_CHIP_STATUS_REP_CHIP_PEND_CMD_ERROR_PEND_BIT) {
            /* 清理还原状态 */
            recv_from_hw_fifo(true);
            rx_buf_recived_size = 0;
            rx_payload_length = 0;
            /* 关闭射频模块PA */
            si446x_pa_enabled(false);
            si446x_trans_led_ctrl(false, false);
            LOG_W("RADIO_CMD_ERROR");
            /* Reset FIFO */
            si446x_fifo_info(SI446X_CMD_FIFO_INFO_ARG_FIFO_TX_BIT | SI446X_CMD_FIFO_INFO_ARG_FIFO_RX_BIT);
            trans_fifo_clear(&rx_fifo);
            /* command error count ++ */
            cmd_err_count ++;
            if (cmd_err_count > CMD_ERR_THRESHOLD_FOR_REINIT) {
                cmd_err_count = 0;
                LOG_E("Radio command error count > %d, reinitialize radio.", CMD_ERR_THRESHOLD_FOR_REINIT);
                radio_hal_init();
            } else {
                /* 重新启动接收 */
                radio_start_rx(pRadioConfiguration->Radio_ChannelNumber, 0u);
            }
            is_sending = false;
            is_recving = false;
        }
        trans_unlock();
    }
}

/**
 * 计算CRC16
 *
 * @param data 计算校验值的数据
 * @param size 校验数据大小
 *
 * @return CRC16结果
 */
static uint16_t calc_crc16(const char *data, size_t size) {
    static const uint8_t auc_crc_hi[] = {
        0x00, 0xC1, 0x81, 0x40, 0x01, 0xC0, 0x80, 0x41, 0x01, 0xC0, 0x80, 0x41,
        0x00, 0xC1, 0x81, 0x40, 0x01, 0xC0, 0x80, 0x41, 0x00, 0xC1, 0x81, 0x40,
        0x00, 0xC1, 0x81, 0x40, 0x01, 0xC0, 0x80, 0x41, 0x01, 0xC0, 0x80, 0x41,
        0x00, 0xC1, 0x81, 0x40, 0x00, 0xC1, 0x81, 0x40, 0x01, 0xC0, 0x80, 0x41,
        0x00, 0xC1, 0x81, 0x40, 0x01, 0xC0, 0x80, 0x41, 0x01, 0xC0, 0x80, 0x41,
        0x00, 0xC1, 0x81, 0x40, 0x01, 0xC0, 0x80, 0x41, 0x00, 0xC1, 0x81, 0x40,
        0x00, 0xC1, 0x81, 0x40, 0x01, 0xC0, 0x80, 0x41, 0x00, 0xC1, 0x81, 0x40,
        0x01, 0xC0, 0x80, 0x41, 0x01, 0xC0, 0x80, 0x41, 0x00, 0xC1, 0x81, 0x40,
        0x00, 0xC1, 0x81, 0x40, 0x01, 0xC0, 0x80, 0x41, 0x01, 0xC0, 0x80, 0x41,
        0x00, 0xC1, 0x81, 0x40, 0x01, 0xC0, 0x80, 0x41, 0x00, 0xC1, 0x81, 0x40,
        0x00, 0xC1, 0x81, 0x40, 0x01, 0xC0, 0x80, 0x41, 0x01, 0xC0, 0x80, 0x41,
        0x00, 0xC1, 0x81, 0x40, 0x00, 0xC1, 0x81, 0x40, 0x01, 0xC0, 0x80, 0x41,
        0x00, 0xC1, 0x81, 0x40, 0x01, 0xC0, 0x80, 0x41, 0x01, 0xC0, 0x80, 0x41,
        0x00, 0xC1, 0x81, 0x40, 0x00, 0xC1, 0x81, 0x40, 0x01, 0xC0, 0x80, 0x41,
        0x01, 0xC0, 0x80, 0x41, 0x00, 0xC1, 0x81, 0x40, 0x01, 0xC0, 0x80, 0x41,
        0x00, 0xC1, 0x81, 0x40, 0x00, 0xC1, 0x81, 0x40, 0x01, 0xC0, 0x80, 0x41,
        0x00, 0xC1, 0x81, 0x40, 0x01, 0xC0, 0x80, 0x41, 0x01, 0xC0, 0x80, 0x41,
        0x00, 0xC1, 0x81, 0x40, 0x01, 0xC0, 0x80, 0x41, 0x00, 0xC1, 0x81, 0x40,
        0x00, 0xC1, 0x81, 0x40, 0x01, 0xC0, 0x80, 0x41, 0x01, 0xC0, 0x80, 0x41,
        0x00, 0xC1, 0x81, 0x40, 0x00, 0xC1, 0x81, 0x40, 0x01, 0xC0, 0x80, 0x41,
        0x00, 0xC1, 0x81, 0x40, 0x01, 0xC0, 0x80, 0x41, 0x01, 0xC0, 0x80, 0x41,
        0x00, 0xC1, 0x81, 0x40
    };

    static const uint8_t auc_crc_lo[] = {
        0x00, 0xC0, 0xC1, 0x01, 0xC3, 0x03, 0x02, 0xC2, 0xC6, 0x06, 0x07, 0xC7,
        0x05, 0xC5, 0xC4, 0x04, 0xCC, 0x0C, 0x0D, 0xCD, 0x0F, 0xCF, 0xCE, 0x0E,
        0x0A, 0xCA, 0xCB, 0x0B, 0xC9, 0x09, 0x08, 0xC8, 0xD8, 0x18, 0x19, 0xD9,
        0x1B, 0xDB, 0xDA, 0x1A, 0x1E, 0xDE, 0xDF, 0x1F, 0xDD, 0x1D, 0x1C, 0xDC,
        0x14, 0xD4, 0xD5, 0x15, 0xD7, 0x17, 0x16, 0xD6, 0xD2, 0x12, 0x13, 0xD3,
        0x11, 0xD1, 0xD0, 0x10, 0xF0, 0x30, 0x31, 0xF1, 0x33, 0xF3, 0xF2, 0x32,
        0x36, 0xF6, 0xF7, 0x37, 0xF5, 0x35, 0x34, 0xF4, 0x3C, 0xFC, 0xFD, 0x3D,
        0xFF, 0x3F, 0x3E, 0xFE, 0xFA, 0x3A, 0x3B, 0xFB, 0x39, 0xF9, 0xF8, 0x38,
        0x28, 0xE8, 0xE9, 0x29, 0xEB, 0x2B, 0x2A, 0xEA, 0xEE, 0x2E, 0x2F, 0xEF,
        0x2D, 0xED, 0xEC, 0x2C, 0xE4, 0x24, 0x25, 0xE5, 0x27, 0xE7, 0xE6, 0x26,
        0x22, 0xE2, 0xE3, 0x23, 0xE1, 0x21, 0x20, 0xE0, 0xA0, 0x60, 0x61, 0xA1,
        0x63, 0xA3, 0xA2, 0x62, 0x66, 0xA6, 0xA7, 0x67, 0xA5, 0x65, 0x64, 0xA4,
        0x6C, 0xAC, 0xAD, 0x6D, 0xAF, 0x6F, 0x6E, 0xAE, 0xAA, 0x6A, 0x6B, 0xAB,
        0x69, 0xA9, 0xA8, 0x68, 0x78, 0xB8, 0xB9, 0x79, 0xBB, 0x7B, 0x7A, 0xBA,
        0xBE, 0x7E, 0x7F, 0xBF, 0x7D, 0xBD, 0xBC, 0x7C, 0xB4, 0x74, 0x75, 0xB5,
        0x77, 0xB7, 0xB6, 0x76, 0x72, 0xB2, 0xB3, 0x73, 0xB1, 0x71, 0x70, 0xB0,
        0x50, 0x90, 0x91, 0x51, 0x93, 0x53, 0x52, 0x92, 0x96, 0x56, 0x57, 0x97,
        0x55, 0x95, 0x94, 0x54, 0x9C, 0x5C, 0x5D, 0x9D, 0x5F, 0x9F, 0x9E, 0x5E,
        0x5A, 0x9A, 0x9B, 0x5B, 0x99, 0x59, 0x58, 0x98, 0x88, 0x48, 0x49, 0x89,
        0x4B, 0x8B, 0x8A, 0x4A, 0x4E, 0x8E, 0x8F, 0x4F, 0x8D, 0x4D, 0x4C, 0x8C,
        0x44, 0x84, 0x85, 0x45, 0x87, 0x47, 0x46, 0x86, 0x82, 0x42, 0x43, 0x83,
        0x41, 0x81, 0x80, 0x40
    };
    uint8_t crc_hi = 0xFF;
    uint8_t crc_lo = 0xFF;
    size_t index;

    while (size--) {
        index = crc_lo ^ *(data++);
        crc_lo = (uint8_t) (crc_hi ^ auc_crc_hi[index]);
        crc_hi = auc_crc_lo[index];
    }
    return (uint16_t) (crc_hi << 8 | crc_lo);
}

#if defined(RT_USING_FINSH) && defined(FINSH_USING_MSH)
#include <finsh.h>

static void si4463(uint8_t argc, char **argv) {

    enum {
        CMD_SEND_INDEX,
        CMD_RECV_INDEX,
        CMD_STAT_INDEX,
        CMD_PROP_INDEX,
        CMD_TEST_INDEX,
    };

    size_t i = 0;

    const char* help_info[] = {
            [CMD_SEND_INDEX]     = "si4463 send <length>            - send some data with length",
            [CMD_RECV_INDEX]     = "si4463 recv                     - receive some data",
            [CMD_STAT_INDEX]     = "si4463 stat                     - show radio transmit statistics",
            [CMD_PROP_INDEX]     = "si4463 prop                     - get or set SI4463 property",
            [CMD_TEST_INDEX]     = "si4463 test <times>             - SI4463 send data test",
    };

    if (argc < 2) {
        rt_kprintf("Usage:\n");
        for (i = 0; i < sizeof(help_info) / sizeof(char*); i++) {
            rt_kprintf("%s\n", help_info[i]);
        }
        rt_kprintf("\n");
    } else {
        const char *operator = argv[1];

        if (!strcmp(operator, "send")) {
            if (argc < 3) {
                rt_kprintf("Usage: %s.\n", help_info[CMD_SEND_INDEX]);
                return;
            }
            size_t len = atoi(argv[2]);
            uint8_t *str = (uint8_t *) rt_malloc(len);
            memset(str, len, len);
            radio_pkt_send(str, len);
            rt_free(str);
        } else if (!strcmp(operator, "recv")) {
            size_t len;
            int rssi;
            uint8_t *str = (uint8_t *) rt_calloc(1, RADIO_TRANS_RX_FIFO_SIZE);
            if (radio_pkt_get_recved(str, RADIO_TRANS_RX_FIFO_SIZE, &len, &rssi) == RT_EOK) {
                rt_kprintf("received %d bytes package, rssi %ddBm\n", len, rssi);
                print_hex(str, len, DBG_INFO);
            } else {
                rt_kprintf("no data, please retry.\n");
            }
            rt_free(str);
        } else if (!strcmp(operator, "stat")) {
            float recv_err_per = 0.0f;
            float send_err_per = 0.0f;
            int rssi = radio_get_latch_rssi();

            if (recv_stat.success_pkt_num + recv_stat.failed_pkt_num) {
                recv_err_per = 100.0f * (float) recv_stat.failed_pkt_num / (float) (recv_stat.success_pkt_num + recv_stat.failed_pkt_num);
            }
            if (send_stat.success_pkt_num + send_stat.failed_pkt_num) {
                send_err_per = 100.0f * (float) send_stat.failed_pkt_num / (float) (send_stat.success_pkt_num + send_stat.failed_pkt_num);
            }

            rt_kprintf("RX packets:%ld errors:%ld (%d.%02d%%) last rssi:%ddBm\n", recv_stat.success_pkt_num,
                    recv_stat.failed_pkt_num, (uint8_t) recv_err_per, (int) (recv_err_per * 100.0f) % 100, rssi);
            rt_kprintf("TX packets:%ld errors:%ld (%d.%02d%%)\n", send_stat.success_pkt_num, send_stat.failed_pkt_num,
                    (uint8_t) send_err_per, (int) (send_err_per * 100.0f) % 100);
            rt_kprintf("RX bytes:%ld (%ld.%01dKiB) TX bytes:%ld (%ld.%01dKiB)\n\n", recv_stat.total_byte,
                    recv_stat.total_byte / 1024, recv_stat.total_byte % 1024 / 100, send_stat.total_byte,
                    send_stat.total_byte / 1024, send_stat.total_byte % 1024 / 100);
        } else if (!strcmp(operator, "prop")) {
//            si446x_set_property(SI446X_PROP_GRP_ID_PKT, 1, SI446X_PROP_GRP_INDEX_PKT_CONFIG1, atoi(argv[2]));
            si446x_get_property(SI446X_PROP_GRP_ID_PKT, 1, SI446X_PROP_GRP_INDEX_PKT_CONFIG1);
            rt_kprintf("SI446X_PROP_GRP_INDEX_PKT_CONFIG1:0x%02X\n", Si446xCmd.GET_PROPERTY.DATA[0]);
//            si446x_set_property(SI446X_PROP_GRP_ID_PKT, 1, SI446X_PROP_GRP_INDEX_PKT_CONFIG2, 0x00);
            si446x_get_property(SI446X_PROP_GRP_ID_PKT, 1, SI446X_PROP_GRP_INDEX_PKT_CONFIG2);
            rt_kprintf("SI446X_PROP_GRP_INDEX_PKT_CONFIG2:0x%02X\n", Si446xCmd.GET_PROPERTY.DATA[0]);
//            si446x_set_property(SI446X_PROP_GRP_ID_PKT, 1, SI446X_PROP_GRP_INDEX_PKT_CRC_CONFIG, atoi(argv[2]));
            si446x_get_property(SI446X_PROP_GRP_ID_PKT, 1, SI446X_PROP_GRP_INDEX_PKT_CRC_CONFIG);
            rt_kprintf("SI446X_PROP_GRP_INDEX_PKT_CRC_CONFIG:0x%02X\n", Si446xCmd.GET_PROPERTY.DATA[0]);
            si446x_get_property(SI446X_PROP_GRP_ID_PKT, 4, SI446X_PROP_GRP_INDEX_PKT_CRC_SEED);
            rt_kprintf("SI446X_PROP_GRP_INDEX_PKT_CRC_SEED:0x%02X%02X%02X%02X\n", Si446xCmd.GET_PROPERTY.DATA[0], Si446xCmd.GET_PROPERTY.DATA[1], Si446xCmd.GET_PROPERTY.DATA[2], Si446xCmd.GET_PROPERTY.DATA[3]);
//            si446x_set_property(SI446X_PROP_GRP_ID_PKT, 1, SI446X_PROP_GRP_INDEX_PKT_FIELD_2_CRC_CONFIG, 0x15);
            si446x_get_property(SI446X_PROP_GRP_ID_PKT, 1, SI446X_PROP_GRP_INDEX_PKT_FIELD_2_CRC_CONFIG);
            rt_kprintf("SI446X_PROP_GRP_INDEX_PKT_FIELD_2_CRC_CONFIG:0x%02X\n", Si446xCmd.GET_PROPERTY.DATA[0]);
//            si446x_set_property(SI446X_PROP_GRP_ID_PKT, 1, SI446X_PROP_GRP_INDEX_PKT_RX_FIELD_2_CRC_CONFIG, 0x15);
            si446x_get_property(SI446X_PROP_GRP_ID_PKT, 1, SI446X_PROP_GRP_INDEX_PKT_RX_FIELD_2_CRC_CONFIG);
            rt_kprintf("SI446X_PROP_GRP_INDEX_PKT_RX_FIELD_2_CRC_CONFIG:0x%02X\n", Si446xCmd.GET_PROPERTY.DATA[0]);
        }  else {
            rt_kprintf("Usage:\n");
            for (i = 0; i < sizeof(help_info) / sizeof(char*); i++) {
                rt_kprintf("%s\n", help_info[i]);
            }
            rt_kprintf("\n");
        }
    }
}
MSH_CMD_EXPORT(si4463, si4463 test. More information by run 'si4463')
#endif
