zengwangfa/Smart-Hive/new_node/bsp/stm32/stm32f405-smdz-breadfruit/board/radio/Si446x/si446x_api_lib.c

/*!
 * File:
 *  si446x_api_lib.c
 *
 * Description:
 *  This file contains the Si446x API library.
 *
 * Silicon Laboratories Confidential
 * Copyright 2011 Silicon Laboratories, Inc.
 */

#include "../radio_comm.h"
#include "../radio_hal.h"
#include "si446x_api_lib.h"
#include <stdarg.h>
#include <rtthread.h>

SEGMENT_VARIABLE( Si446xCmd, union si446x_cmd_reply_union, SEG_XDATA );
SEGMENT_VARIABLE( Pro2Cmd[16], U8, SEG_XDATA );

#ifdef SI446X_PATCH_CMDS
SEGMENT_VARIABLE( Si446xPatchCommands[][8] = { SI446X_PATCH_CMDS }, U8, SEG_CODE);
#endif


/*!
 * This functions is used to reset the si446x radio by applying shutdown and
 * releasing it.  After this function @ref si446x_boot should be called.  You
 * can check if POR has completed by waiting 4 ms or by polling GPIO 0, 2, or 3.
 * When these GPIOs are high, it is safe to call @ref si446x_boot.
 */
void si446x_reset(void)
{
    /* Put radio in shutdown, wait then release */
    radio_hal_AssertShutdown();
    rt_thread_delay(rt_tick_from_millisecond(5));
    radio_hal_DeassertShutdown();
    rt_thread_delay(rt_tick_from_millisecond(5));
    radio_comm_ClearCTS();
}

/*!
 * This function is used to initialize after power-up the radio chip.
 * Before this function @si446x_reset should be called.
 */
void si446x_power_up(U8 BOOT_OPTIONS, U8 XTAL_OPTIONS, U32 XO_FREQ)
{
    Pro2Cmd[0] = SI446X_CMD_ID_POWER_UP;
    Pro2Cmd[1] = BOOT_OPTIONS;
    Pro2Cmd[2] = XTAL_OPTIONS;
    Pro2Cmd[3] = (U8)(XO_FREQ >> 24);
    Pro2Cmd[4] = (U8)(XO_FREQ >> 16);
    Pro2Cmd[5] = (U8)(XO_FREQ >> 8);
    Pro2Cmd[6] = (U8)(XO_FREQ);

    radio_comm_SendCmd( SI446X_CMD_ARG_COUNT_POWER_UP, Pro2Cmd );
}

/*!
 * This function is used to load all properties and commands with a list of NULL terminated commands.
 * Before this function @si446x_reset should be called.
 */
U8 si446x_configuration_init(const U8* pSetPropCmd)
{
  SEGMENT_VARIABLE(col, U8, SEG_DATA);
  SEGMENT_VARIABLE(numOfBytes, U8, SEG_DATA);

  /* While cycle as far as the pointer points to a command */
  while (*pSetPropCmd != 0x00)
  {
    /* Commands structure in the array:
     * --------------------------------
     * LEN | <LEN length of data>
     */

    numOfBytes = *pSetPropCmd++;

    if (numOfBytes > 16u)
    {
      /* Number of command bytes exceeds maximal allowable length */
      return SI446X_COMMAND_ERROR;
    }

    for (col = 0u; col < numOfBytes; col++)
    {
      Pro2Cmd[col] = *pSetPropCmd;
      pSetPropCmd++;
    }

    if (radio_comm_SendCmdGetResp(numOfBytes, Pro2Cmd, 0, 0) != 0xFF)
    {
      /* Timeout occured */
      return SI446X_CTS_TIMEOUT;
    }

    if (radio_hal_NirqLevel() == 0)
    {
      /* Get and clear all interrupts.  An error has occured... */
      si446x_get_int_status(0, 0, 0);
      if (Si446xCmd.GET_INT_STATUS.CHIP_PEND & SI446X_CMD_GET_CHIP_STATUS_REP_CHIP_PEND_CMD_ERROR_PEND_MASK)
      {
        return SI446X_COMMAND_ERROR;
      }
    }
  }

  return SI446X_SUCCESS;
}

/*! This function sends the PART_INFO command to the radio and receives the answer
 *  into @Si446xCmd union.
 */
void si446x_part_info(void)
{
    Pro2Cmd[0] = SI446X_CMD_ID_PART_INFO;

    radio_comm_SendCmdGetResp( SI446X_CMD_ARG_COUNT_PART_INFO,
                              Pro2Cmd,
                              SI446X_CMD_REPLY_COUNT_PART_INFO,
                              Pro2Cmd );

    Si446xCmd.PART_INFO.CHIPREV         = Pro2Cmd[0];
    Si446xCmd.PART_INFO.PART            = ((U16)Pro2Cmd[1] << 8) & 0xFF00;
    Si446xCmd.PART_INFO.PART           |= (U16)Pro2Cmd[2] & 0x00FF;
    Si446xCmd.PART_INFO.PBUILD          = Pro2Cmd[3];
    Si446xCmd.PART_INFO.ID              = ((U16)Pro2Cmd[4] << 8) & 0xFF00;
    Si446xCmd.PART_INFO.ID             |= (U16)Pro2Cmd[5] & 0x00FF;
    Si446xCmd.PART_INFO.CUSTOMER        = Pro2Cmd[6];
    Si446xCmd.PART_INFO.ROMID           = Pro2Cmd[7];
}

/*! Sends START_TX command to the radio.
 *
 * @param CHANNEL   Channel number.
 * @param CONDITION Start TX condition.
 * @param TX_LEN    Payload length (exclude the PH generated CRC).
 */
void si446x_start_tx(U8 CHANNEL, U8 CONDITION, U16 TX_LEN)
{
    Pro2Cmd[0] = SI446X_CMD_ID_START_TX;
    Pro2Cmd[1] = CHANNEL;
    Pro2Cmd[2] = CONDITION;
    Pro2Cmd[3] = (U8)(TX_LEN >> 8);
    Pro2Cmd[4] = (U8)(TX_LEN);
    Pro2Cmd[5] = 0x00;

    // Don't repeat the packet, 
    // ie. transmit the packet only once
    Pro2Cmd[6] = 0x00;

    radio_comm_SendCmd( SI446X_CMD_ARG_COUNT_START_TX, Pro2Cmd );
}

/*!
 * Sends START_RX command to the radio.
 *
 * @param CHANNEL     Channel number.
 * @param CONDITION   Start RX condition.
 * @param RX_LEN      Payload length (exclude the PH generated CRC).
 * @param NEXT_STATE1 Next state when Preamble Timeout occurs.
 * @param NEXT_STATE2 Next state when a valid packet received.
 * @param NEXT_STATE3 Next state when invalid packet received (e.g. CRC error).
 */
void si446x_start_rx(U8 CHANNEL, U8 CONDITION, U16 RX_LEN, U8 NEXT_STATE1, U8 NEXT_STATE2, U8 NEXT_STATE3)
{
    Pro2Cmd[0] = SI446X_CMD_ID_START_RX;
    Pro2Cmd[1] = CHANNEL;
    Pro2Cmd[2] = CONDITION;
    Pro2Cmd[3] = (U8)(RX_LEN >> 8);
    Pro2Cmd[4] = (U8)(RX_LEN);
    Pro2Cmd[5] = NEXT_STATE1;
    Pro2Cmd[6] = NEXT_STATE2;
    Pro2Cmd[7] = NEXT_STATE3;

    radio_comm_SendCmd( SI446X_CMD_ARG_COUNT_START_RX, Pro2Cmd );
}

/*!
 * Get the Interrupt status/pending flags form the radio and clear flags if requested.
 *
 * @param PH_CLR_PEND     Packet Handler pending flags clear.
 * @param MODEM_CLR_PEND  Modem Status pending flags clear.
 * @param CHIP_CLR_PEND   Chip State pending flags clear.
 */
void si446x_get_int_status(U8 PH_CLR_PEND, U8 MODEM_CLR_PEND, U8 CHIP_CLR_PEND)
{
    Pro2Cmd[0] = SI446X_CMD_ID_GET_INT_STATUS;
    Pro2Cmd[1] = PH_CLR_PEND;
    Pro2Cmd[2] = MODEM_CLR_PEND;
    Pro2Cmd[3] = CHIP_CLR_PEND;

    radio_comm_SendCmdGetResp( SI446X_CMD_ARG_COUNT_GET_INT_STATUS,
                              Pro2Cmd,
                              SI446X_CMD_REPLY_COUNT_GET_INT_STATUS,
                              Pro2Cmd );

    Si446xCmd.GET_INT_STATUS.INT_PEND       = Pro2Cmd[0];
    Si446xCmd.GET_INT_STATUS.INT_STATUS     = Pro2Cmd[1];
    Si446xCmd.GET_INT_STATUS.PH_PEND        = Pro2Cmd[2];
    Si446xCmd.GET_INT_STATUS.PH_STATUS      = Pro2Cmd[3];
    Si446xCmd.GET_INT_STATUS.MODEM_PEND     = Pro2Cmd[4];
    Si446xCmd.GET_INT_STATUS.MODEM_STATUS   = Pro2Cmd[5];
    Si446xCmd.GET_INT_STATUS.CHIP_PEND      = Pro2Cmd[6];
    Si446xCmd.GET_INT_STATUS.CHIP_STATUS    = Pro2Cmd[7];
}

/*!
 * Send GPIO pin config command to the radio and reads the answer into
 * @Si446xCmd union.
 *
 * @param GPIO0       GPIO0 configuration.
 * @param GPIO1       GPIO1 configuration.
 * @param GPIO2       GPIO2 configuration.
 * @param GPIO3       GPIO3 configuration.
 * @param NIRQ        NIRQ configuration.
 * @param SDO         SDO configuration.
 * @param GEN_CONFIG  General pin configuration.
 */
void si446x_gpio_pin_cfg(U8 GPIO0, U8 GPIO1, U8 GPIO2, U8 GPIO3, U8 NIRQ, U8 SDO, U8 GEN_CONFIG)
{
    Pro2Cmd[0] = SI446X_CMD_ID_GPIO_PIN_CFG;
    Pro2Cmd[1] = GPIO0;
    Pro2Cmd[2] = GPIO1;
    Pro2Cmd[3] = GPIO2;
    Pro2Cmd[4] = GPIO3;
    Pro2Cmd[5] = NIRQ;
    Pro2Cmd[6] = SDO;
    Pro2Cmd[7] = GEN_CONFIG;

    radio_comm_SendCmdGetResp( SI446X_CMD_ARG_COUNT_GPIO_PIN_CFG,
                              Pro2Cmd,
                              SI446X_CMD_REPLY_COUNT_GPIO_PIN_CFG,
                              Pro2Cmd );

    Si446xCmd.GPIO_PIN_CFG.GPIO[0]        = Pro2Cmd[0];
    Si446xCmd.GPIO_PIN_CFG.GPIO[1]        = Pro2Cmd[1];
    Si446xCmd.GPIO_PIN_CFG.GPIO[2]        = Pro2Cmd[2];
    Si446xCmd.GPIO_PIN_CFG.GPIO[3]        = Pro2Cmd[3];
    Si446xCmd.GPIO_PIN_CFG.NIRQ         = Pro2Cmd[4];
    Si446xCmd.GPIO_PIN_CFG.SDO          = Pro2Cmd[5];
    Si446xCmd.GPIO_PIN_CFG.GEN_CONFIG   = Pro2Cmd[6];
}

/*!
 * Send SET_PROPERTY command to the radio.
 *
 * @param GROUP       Property group.
 * @param NUM_PROPS   Number of property to be set. The properties must be in ascending order
 *                    in their sub-property aspect. Max. 12 properties can be set in one command.
 * @param START_PROP  Start sub-property address.
 */
#ifdef __C51__
#pragma maxargs (13)  /* allow 13 bytes for parameters */
#endif
void si446x_set_property( U8 GROUP, U8 NUM_PROPS, U8 START_PROP, ... )
{
    va_list argList;
    U8 cmdIndex;

    Pro2Cmd[0] = SI446X_CMD_ID_SET_PROPERTY;
    Pro2Cmd[1] = GROUP;
    Pro2Cmd[2] = NUM_PROPS;
    Pro2Cmd[3] = START_PROP;

    va_start (argList, START_PROP);
    cmdIndex = 4;
    while(NUM_PROPS--)
    {
        Pro2Cmd[cmdIndex] = va_arg (argList, int);
        cmdIndex++;
    }
    va_end(argList);

    radio_comm_SendCmd( cmdIndex, Pro2Cmd );
}

/*!
 * Issue a change state command to the radio.
 *
 * @param NEXT_STATE1 Next state.
 */
void si446x_change_state(U8 NEXT_STATE1)
{
    Pro2Cmd[0] = SI446X_CMD_ID_CHANGE_STATE;
    Pro2Cmd[1] = NEXT_STATE1;

    radio_comm_SendCmd( SI446X_CMD_ARG_COUNT_CHANGE_STATE, Pro2Cmd );
}


#ifdef RADIO_DRIVER_EXTENDED_SUPPORT
/* Extended driver support functions */
/*!
 * Sends NOP command to the radio. Can be used to maintain SPI communication.
 */
void si446x_nop(void)
{
    Pro2Cmd[0] = SI446X_CMD_ID_NOP;

    radio_comm_SendCmd( SI446X_CMD_ARG_COUNT_NOP, Pro2Cmd );
}

/*!
 * Send the FIFO_INFO command to the radio. Optionally resets the TX/RX FIFO. Reads the radio response back
 * into @Si446xCmd.
 *
 * @param FIFO  RX/TX FIFO reset flags.
 */
void si446x_fifo_info(U8 FIFO)
{
    Pro2Cmd[0] = SI446X_CMD_ID_FIFO_INFO;
    Pro2Cmd[1] = FIFO;

    radio_comm_SendCmdGetResp( SI446X_CMD_ARG_COUNT_FIFO_INFO,
                              Pro2Cmd,
                              SI446X_CMD_REPLY_COUNT_FIFO_INFO,
                              Pro2Cmd );

    Si446xCmd.FIFO_INFO.RX_FIFO_COUNT   = Pro2Cmd[0];
    Si446xCmd.FIFO_INFO.TX_FIFO_SPACE   = Pro2Cmd[1];
}

/*!
 * The function can be used to load data into TX FIFO.
 *
 * @param numBytes  Data length to be load.
 * @param pTxData   Pointer to the data (U8*).
 */
void si446x_write_tx_fifo(U8 numBytes, U8* pTxData)
{
  radio_comm_WriteData( SI446X_CMD_ID_WRITE_TX_FIFO, 0, numBytes, pTxData );
}

/*!
 * Reads the RX FIFO content from the radio.
 *
 * @param numBytes  Data length to be read.
 * @param pRxData   Pointer to the buffer location.
 */
void si446x_read_rx_fifo(U8 numBytes, U8* pRxData)
{
  radio_comm_ReadData( SI446X_CMD_ID_READ_RX_FIFO, 0, numBytes, pRxData );
}

/*!
 * Get property values from the radio. Reads them into Si446xCmd union.
 *
 * @param GROUP       Property group number.
 * @param NUM_PROPS   Number of properties to be read.
 * @param START_PROP  Starting sub-property number.
 */
void si446x_get_property(U8 GROUP, U8 NUM_PROPS, U8 START_PROP)
{
    Pro2Cmd[0] = SI446X_CMD_ID_GET_PROPERTY;
    Pro2Cmd[1] = GROUP;
    Pro2Cmd[2] = NUM_PROPS;
    Pro2Cmd[3] = START_PROP;

    radio_comm_SendCmdGetResp( SI446X_CMD_ARG_COUNT_GET_PROPERTY,
                              Pro2Cmd,
                              Pro2Cmd[2],
                              Pro2Cmd );

    Si446xCmd.GET_PROPERTY.DATA[0 ]   = Pro2Cmd[0];
    Si446xCmd.GET_PROPERTY.DATA[1 ]   = Pro2Cmd[1];
    Si446xCmd.GET_PROPERTY.DATA[2 ]   = Pro2Cmd[2];
    Si446xCmd.GET_PROPERTY.DATA[3 ]   = Pro2Cmd[3];
    Si446xCmd.GET_PROPERTY.DATA[4 ]   = Pro2Cmd[4];
    Si446xCmd.GET_PROPERTY.DATA[5 ]   = Pro2Cmd[5];
    Si446xCmd.GET_PROPERTY.DATA[6 ]   = Pro2Cmd[6];
    Si446xCmd.GET_PROPERTY.DATA[7 ]   = Pro2Cmd[7];
    Si446xCmd.GET_PROPERTY.DATA[8 ]   = Pro2Cmd[8];
    Si446xCmd.GET_PROPERTY.DATA[9 ]   = Pro2Cmd[9];
    Si446xCmd.GET_PROPERTY.DATA[10]   = Pro2Cmd[10];
    Si446xCmd.GET_PROPERTY.DATA[11]   = Pro2Cmd[11];
    Si446xCmd.GET_PROPERTY.DATA[12]   = Pro2Cmd[12];
    Si446xCmd.GET_PROPERTY.DATA[13]   = Pro2Cmd[13];
    Si446xCmd.GET_PROPERTY.DATA[14]   = Pro2Cmd[14];
    Si446xCmd.GET_PROPERTY.DATA[15]   = Pro2Cmd[15];
}


#ifdef RADIO_DRIVER_FULL_SUPPORT
/* Full driver support functions */

/*!
 * Sends the FUNC_INFO command to the radio, then reads the resonse into @Si446xCmd union.
 */
void si446x_func_info(void)
{
    Pro2Cmd[0] = SI446X_CMD_ID_FUNC_INFO;

    radio_comm_SendCmdGetResp( SI446X_CMD_ARG_COUNT_FUNC_INFO,
                              Pro2Cmd,
                              SI446X_CMD_REPLY_COUNT_FUNC_INFO,
                              Pro2Cmd );

    Si446xCmd.FUNC_INFO.REVEXT          = Pro2Cmd[0];
    Si446xCmd.FUNC_INFO.REVBRANCH       = Pro2Cmd[1];
    Si446xCmd.FUNC_INFO.REVINT          = Pro2Cmd[2];
    Si446xCmd.FUNC_INFO.FUNC            = Pro2Cmd[5];
}

/*!
 * Reads the Fast Response Registers starting with A register into @Si446xCmd union.
 *
 * @param respByteCount Number of Fast Response Registers to be read.
 */
void si446x_frr_a_read(U8 respByteCount)
{
    radio_comm_ReadData(SI446X_CMD_ID_FRR_A_READ,
                            0,
                        respByteCount,
                        Pro2Cmd);

    Si446xCmd.FRR_A_READ.FRR_A_VALUE = Pro2Cmd[0];
    Si446xCmd.FRR_A_READ.FRR_B_VALUE = Pro2Cmd[1];
    Si446xCmd.FRR_A_READ.FRR_C_VALUE = Pro2Cmd[2];
    Si446xCmd.FRR_A_READ.FRR_D_VALUE = Pro2Cmd[3];
}

/*!
 * Reads the Fast Response Registers starting with B register into @Si446xCmd union.
 *
 * @param respByteCount Number of Fast Response Registers to be read.
 */
void si446x_frr_b_read(U8 respByteCount)
{
    radio_comm_ReadData(SI446X_CMD_ID_FRR_B_READ,
                            0,
                        respByteCount,
                        Pro2Cmd);

    Si446xCmd.FRR_B_READ.FRR_B_VALUE = Pro2Cmd[0];
    Si446xCmd.FRR_B_READ.FRR_C_VALUE = Pro2Cmd[1];
    Si446xCmd.FRR_B_READ.FRR_D_VALUE = Pro2Cmd[2];
    Si446xCmd.FRR_B_READ.FRR_A_VALUE = Pro2Cmd[3];
}

/*!
 * Reads the Fast Response Registers starting with C register into @Si446xCmd union.
 *
 * @param respByteCount Number of Fast Response Registers to be read.
 */
void si446x_frr_c_read(U8 respByteCount)
{
    radio_comm_ReadData(SI446X_CMD_ID_FRR_C_READ,
                            0,
                        respByteCount,
                        Pro2Cmd);

    Si446xCmd.FRR_C_READ.FRR_C_VALUE = Pro2Cmd[0];
    Si446xCmd.FRR_C_READ.FRR_D_VALUE = Pro2Cmd[1];
    Si446xCmd.FRR_C_READ.FRR_A_VALUE = Pro2Cmd[2];
    Si446xCmd.FRR_C_READ.FRR_B_VALUE = Pro2Cmd[3];
}

/*!
 * Reads the Fast Response Registers starting with D register into @Si446xCmd union.
 *
 * @param respByteCount Number of Fast Response Registers to be read.
 */
void si446x_frr_d_read(U8 respByteCount)
{
    radio_comm_ReadData(SI446X_CMD_ID_FRR_D_READ,
                            0,
                        respByteCount,
                        Pro2Cmd);

    Si446xCmd.FRR_D_READ.FRR_D_VALUE = Pro2Cmd[0];
    Si446xCmd.FRR_D_READ.FRR_A_VALUE = Pro2Cmd[1];
    Si446xCmd.FRR_D_READ.FRR_B_VALUE = Pro2Cmd[2];
    Si446xCmd.FRR_D_READ.FRR_C_VALUE = Pro2Cmd[3];
}

/*!
 * Reads the ADC values from the radio into @Si446xCmd union.
 *
 * @param ADC_EN  ADC enable parameter.
 */
void si446x_get_adc_reading(U8 ADC_EN)
{
    Pro2Cmd[0] = SI446X_CMD_ID_GET_ADC_READING;
    Pro2Cmd[1] = ADC_EN;

    radio_comm_SendCmdGetResp( SI446X_CMD_ARG_COUNT_GET_ADC_READING,
                              Pro2Cmd,
                              SI446X_CMD_REPLY_COUNT_GET_ADC_READING,
                              Pro2Cmd );

    Si446xCmd.GET_ADC_READING.GPIO_ADC         = ((U16)Pro2Cmd[0] << 8) & 0xFF00;
    Si446xCmd.GET_ADC_READING.GPIO_ADC        |=  (U16)Pro2Cmd[1] & 0x00FF;
    Si446xCmd.GET_ADC_READING.BATTERY_ADC      = ((U16)Pro2Cmd[2] << 8) & 0xFF00;
    Si446xCmd.GET_ADC_READING.BATTERY_ADC     |=  (U16)Pro2Cmd[3] & 0x00FF;
    Si446xCmd.GET_ADC_READING.TEMP_ADC         = ((U16)Pro2Cmd[4] << 8) & 0xFF00;
    Si446xCmd.GET_ADC_READING.TEMP_ADC        |=  (U16)Pro2Cmd[5] & 0x00FF;
}

/*!
 * Receives information from the radio of the current packet. Optionally can be used to modify
 * the Packet Handler properties during packet reception.
 *
 * @param FIELD_NUMBER_MASK Packet Field number mask value.
 * @param LEN               Length value.
 * @param DIFF_LEN          Difference length.
 */
void si446x_get_packet_info(U8 FIELD_NUMBER_MASK, U16 LEN, S16 DIFF_LEN )
{
    Pro2Cmd[0] = SI446X_CMD_ID_PACKET_INFO;
    Pro2Cmd[1] = FIELD_NUMBER_MASK;
    Pro2Cmd[2] = (U8)(LEN >> 8);
    Pro2Cmd[3] = (U8)(LEN);
    // the different of the byte, althrough it is signed, but to command hander
    // it can treat it as unsigned
    Pro2Cmd[4] = (U8)((U16)DIFF_LEN >> 8);
    Pro2Cmd[5] = (U8)(DIFF_LEN);

    radio_comm_SendCmdGetResp( SI446X_CMD_ARG_COUNT_PACKET_INFO,
                              Pro2Cmd,
                              SI446X_CMD_REPLY_COUNT_PACKET_INFO,
                              Pro2Cmd );

    Si446xCmd.PACKET_INFO.LENGTH = ((U16)Pro2Cmd[0] << 8) & 0xFF00;
    Si446xCmd.PACKET_INFO.LENGTH |= (U16)Pro2Cmd[1] & 0x00FF;
}

/*!
 * Gets the Packet Handler status flags. Optionally clears them.
 *
 * @param PH_CLR_PEND Flags to clear.
 */
void si446x_get_ph_status(U8 PH_CLR_PEND)
{
    Pro2Cmd[0] = SI446X_CMD_ID_GET_PH_STATUS;
    Pro2Cmd[1] = PH_CLR_PEND;

    radio_comm_SendCmdGetResp( SI446X_CMD_ARG_COUNT_GET_PH_STATUS,
                              Pro2Cmd,
                              SI446X_CMD_REPLY_COUNT_GET_PH_STATUS,
                              Pro2Cmd );

    Si446xCmd.GET_PH_STATUS.PH_PEND        = Pro2Cmd[0];
    Si446xCmd.GET_PH_STATUS.PH_STATUS      = Pro2Cmd[1];
}

/*!
 * Gets the Modem status flags. Optionally clears them.
 *
 * @param MODEM_CLR_PEND Flags to clear.
 */
void si446x_get_modem_status( U8 MODEM_CLR_PEND )
{
    Pro2Cmd[0] = SI446X_CMD_ID_GET_MODEM_STATUS;
    Pro2Cmd[1] = MODEM_CLR_PEND;

    radio_comm_SendCmdGetResp( SI446X_CMD_ARG_COUNT_GET_MODEM_STATUS,
                              Pro2Cmd,
                              SI446X_CMD_REPLY_COUNT_GET_MODEM_STATUS,
                              Pro2Cmd );

    Si446xCmd.GET_MODEM_STATUS.MODEM_PEND   = Pro2Cmd[0];
    Si446xCmd.GET_MODEM_STATUS.MODEM_STATUS = Pro2Cmd[1];
    Si446xCmd.GET_MODEM_STATUS.CURR_RSSI    = Pro2Cmd[2];
    Si446xCmd.GET_MODEM_STATUS.LATCH_RSSI   = Pro2Cmd[3];
    Si446xCmd.GET_MODEM_STATUS.ANT1_RSSI    = Pro2Cmd[4];
    Si446xCmd.GET_MODEM_STATUS.ANT2_RSSI    = Pro2Cmd[5];
    Si446xCmd.GET_MODEM_STATUS.AFC_FREQ_OFFSET =  ((U16)Pro2Cmd[6] << 8) & 0xFF00;
    Si446xCmd.GET_MODEM_STATUS.AFC_FREQ_OFFSET |= (U16)Pro2Cmd[7] & 0x00FF;
}

/*!
 * Gets the Chip status flags. Optionally clears them.
 *
 * @param CHIP_CLR_PEND Flags to clear.
 */
void si446x_get_chip_status( U8 CHIP_CLR_PEND )
{
    Pro2Cmd[0] = SI446X_CMD_ID_GET_CHIP_STATUS;
    Pro2Cmd[1] = CHIP_CLR_PEND;

    radio_comm_SendCmdGetResp( SI446X_CMD_ARG_COUNT_GET_CHIP_STATUS,
                              Pro2Cmd,
                              SI446X_CMD_REPLY_COUNT_GET_CHIP_STATUS,
                              Pro2Cmd );

    Si446xCmd.GET_CHIP_STATUS.CHIP_PEND         = Pro2Cmd[0];
    Si446xCmd.GET_CHIP_STATUS.CHIP_STATUS       = Pro2Cmd[1];
    Si446xCmd.GET_CHIP_STATUS.CMD_ERR_STATUS    = Pro2Cmd[2];
}

/*!
 * Performs image rejection calibration. Completion can be monitored by polling CTS or waiting for CHIP_READY interrupt source.
 *
 * @param SEARCHING_STEP_SIZE
 * @param SEARCHING_RSSI_AVG
 * @param RX_CHAIN_SETTING1
 * @param RX_CHAIN_SETTING2
 */
void si446x_ircal(U8 SEARCHING_STEP_SIZE, U8 SEARCHING_RSSI_AVG, U8 RX_CHAIN_SETTING1, U8 RX_CHAIN_SETTING2)
{
    Pro2Cmd[0] = SI446X_CMD_ID_IRCAL;
    Pro2Cmd[1] = SEARCHING_STEP_SIZE;
    Pro2Cmd[2] = SEARCHING_RSSI_AVG;
    Pro2Cmd[3] = RX_CHAIN_SETTING1;
    Pro2Cmd[4] = RX_CHAIN_SETTING2;

    radio_comm_SendCmd( SI446X_CMD_ARG_COUNT_IRCAL, Pro2Cmd);
}


/*!
 * Image rejection calibration. Forces a specific value for IR calibration, and reads back calibration values from previous calibrations
 *
 * @param IRCAL_AMP
 * @param IRCAL_PH
 */
void si446x_ircal_manual(U8 IRCAL_AMP, U8 IRCAL_PH)
{
    Pro2Cmd[0] = SI446X_CMD_ID_IRCAL_MANUAL;
    Pro2Cmd[1] = IRCAL_AMP;
    Pro2Cmd[2] = IRCAL_PH;

    radio_comm_SendCmdGetResp( SI446X_CMD_ARG_COUNT_IRCAL_MANUAL,
                              Pro2Cmd,
                              SI446X_CMD_REPLY_COUNT_IRCAL_MANUAL,
                              Pro2Cmd );

    Si446xCmd.IRCAL_MANUAL.IRCAL_AMP_REPLY   = Pro2Cmd[0];
    Si446xCmd.IRCAL_MANUAL.IRCAL_PH_REPLY    = Pro2Cmd[1];
}

/*!
 * Requests the current state of the device and lists pending TX and RX requests
 */
void si446x_request_device_state(void)
{
    Pro2Cmd[0] = SI446X_CMD_ID_REQUEST_DEVICE_STATE;

    radio_comm_SendCmdGetResp( SI446X_CMD_ARG_COUNT_REQUEST_DEVICE_STATE,
                              Pro2Cmd,
                              SI446X_CMD_REPLY_COUNT_REQUEST_DEVICE_STATE,
                              Pro2Cmd );

    Si446xCmd.REQUEST_DEVICE_STATE.CURR_STATE       = Pro2Cmd[0];
    Si446xCmd.REQUEST_DEVICE_STATE.CURRENT_CHANNEL  = Pro2Cmd[1];
}

/*!
 * While in TX state this will hop to the frequency specified by the parameters
 *
 * @param INTE      New INTE register value.
 * @param FRAC2     New FRAC2 register value.
 * @param FRAC1     New FRAC1 register value.
 * @param FRAC0     New FRAC0 register value.
 * @param VCO_CNT1  New VCO_CNT1 register value.
 * @param VCO_CNT0  New VCO_CNT0 register value.
 * @param PLL_SETTLE_TIME1  New PLL_SETTLE_TIME1 register value.
 * @param PLL_SETTLE_TIME0  New PLL_SETTLE_TIME0 register value.
 */
void si446x_tx_hop(U8 INTE, U8 FRAC2, U8 FRAC1, U8 FRAC0, U8 VCO_CNT1, U8 VCO_CNT0, U8 PLL_SETTLE_TIME1, U8 PLL_SETTLE_TIME0)
{
    Pro2Cmd[0] = SI446X_CMD_ID_TX_HOP;
    Pro2Cmd[1] = INTE;
    Pro2Cmd[2] = FRAC2;
    Pro2Cmd[3] = FRAC1;
    Pro2Cmd[4] = FRAC0;
    Pro2Cmd[5] = VCO_CNT1;
    Pro2Cmd[6] = VCO_CNT0;
    Pro2Cmd[7] = PLL_SETTLE_TIME1;
    Pro2Cmd[8] = PLL_SETTLE_TIME0;

    radio_comm_SendCmd( SI446X_CMD_ARG_COUNT_TX_HOP, Pro2Cmd );
}

/*!
 * While in RX state this will hop to the frequency specified by the parameters and start searching for a preamble.
 *
 * @param INTE      New INTE register value.
 * @param FRAC2     New FRAC2 register value.
 * @param FRAC1     New FRAC1 register value.
 * @param FRAC0     New FRAC0 register value.
 * @param VCO_CNT1  New VCO_CNT1 register value.
 * @param VCO_CNT0  New VCO_CNT0 register value.
 */
void si446x_rx_hop(U8 INTE, U8 FRAC2, U8 FRAC1, U8 FRAC0, U8 VCO_CNT1, U8 VCO_CNT0)
{
    Pro2Cmd[0] = SI446X_CMD_ID_RX_HOP;
    Pro2Cmd[1] = INTE;
    Pro2Cmd[2] = FRAC2;
    Pro2Cmd[3] = FRAC1;
    Pro2Cmd[4] = FRAC0;
    Pro2Cmd[5] = VCO_CNT1;
    Pro2Cmd[6] = VCO_CNT0;

    radio_comm_SendCmd( SI446X_CMD_ARG_COUNT_RX_HOP, Pro2Cmd );
}

/*! Sends START_TX command ID to the radio with no input parameters
 *
 */
void si446x_start_tx_fast( void )
{
    Pro2Cmd[0] = SI446X_CMD_ID_START_TX;

    radio_comm_SendCmd( 1, Pro2Cmd );
}

/*!
 * Sends START_RX command ID to the radio with no input parameters
 *
 */
void si446x_start_rx_fast( void )
{
    Pro2Cmd[0] = SI446X_CMD_ID_START_RX;

    radio_comm_SendCmd( 1, Pro2Cmd );
}

/*!
 * Clear all Interrupt status/pending flags. Does NOT read back interrupt flags
 *
 */
void si446x_get_int_status_fast_clear( void )
{
    Pro2Cmd[0] = SI446X_CMD_ID_GET_INT_STATUS;

    radio_comm_SendCmd( 1, Pro2Cmd );
}

/*!
 * Clear and read all Interrupt status/pending flags
 *
 */
void si446x_get_int_status_fast_clear_read(void)
{
    Pro2Cmd[0] = SI446X_CMD_ID_GET_INT_STATUS;

    radio_comm_SendCmdGetResp( 1,
                              Pro2Cmd,
                              SI446X_CMD_REPLY_COUNT_GET_INT_STATUS,
                              Pro2Cmd );

    Si446xCmd.GET_INT_STATUS.INT_PEND       = Pro2Cmd[0];
    Si446xCmd.GET_INT_STATUS.INT_STATUS     = Pro2Cmd[1];
    Si446xCmd.GET_INT_STATUS.PH_PEND        = Pro2Cmd[2];
    Si446xCmd.GET_INT_STATUS.PH_STATUS      = Pro2Cmd[3];
    Si446xCmd.GET_INT_STATUS.MODEM_PEND     = Pro2Cmd[4];
    Si446xCmd.GET_INT_STATUS.MODEM_STATUS   = Pro2Cmd[5];
    Si446xCmd.GET_INT_STATUS.CHIP_PEND      = Pro2Cmd[6];
    Si446xCmd.GET_INT_STATUS.CHIP_STATUS    = Pro2Cmd[7];
}

/*!
 * Reads back current GPIO pin configuration. Does NOT configure GPIO pins
  *
 */
void si446x_gpio_pin_cfg_fast( void )
{
    Pro2Cmd[0] = SI446X_CMD_ID_GPIO_PIN_CFG;

    radio_comm_SendCmdGetResp( 1,
                              Pro2Cmd,
                              SI446X_CMD_REPLY_COUNT_GPIO_PIN_CFG,
                              Pro2Cmd );

    Si446xCmd.GPIO_PIN_CFG.GPIO[0]        = Pro2Cmd[0];
    Si446xCmd.GPIO_PIN_CFG.GPIO[1]        = Pro2Cmd[1];
    Si446xCmd.GPIO_PIN_CFG.GPIO[2]        = Pro2Cmd[2];
    Si446xCmd.GPIO_PIN_CFG.GPIO[3]        = Pro2Cmd[3];
    Si446xCmd.GPIO_PIN_CFG.NIRQ         = Pro2Cmd[4];
    Si446xCmd.GPIO_PIN_CFG.SDO          = Pro2Cmd[5];
    Si446xCmd.GPIO_PIN_CFG.GEN_CONFIG   = Pro2Cmd[6];
}


/*!
 * Clear all Packet Handler status flags. Does NOT read back interrupt flags
 *
 */
void si446x_get_ph_status_fast_clear( void )
{
    Pro2Cmd[0] = SI446X_CMD_ID_GET_PH_STATUS;
    Pro2Cmd[1] = 0;

    radio_comm_SendCmd( 2, Pro2Cmd );
}

/*!
 * Clear and read all Packet Handler status flags.
 *
 */
void si446x_get_ph_status_fast_clear_read(void)
{
    Pro2Cmd[0] = SI446X_CMD_ID_GET_PH_STATUS;

    radio_comm_SendCmdGetResp( 1,
                              Pro2Cmd,
                              SI446X_CMD_REPLY_COUNT_GET_PH_STATUS,
                              Pro2Cmd );

    Si446xCmd.GET_PH_STATUS.PH_PEND        = Pro2Cmd[0];
    Si446xCmd.GET_PH_STATUS.PH_STATUS      = Pro2Cmd[1];
}

/*!
 * Clear all Modem status flags. Does NOT read back interrupt flags
 *
 */
void si446x_get_modem_status_fast_clear( void )
{
    Pro2Cmd[0] = SI446X_CMD_ID_GET_MODEM_STATUS;
    Pro2Cmd[1] = 0;

    radio_comm_SendCmd( 2, Pro2Cmd );
}

/*!
 * Clear and read all Modem status flags.
 *
 */
void si446x_get_modem_status_fast_clear_read( void )
{
    Pro2Cmd[0] = SI446X_CMD_ID_GET_MODEM_STATUS;

    radio_comm_SendCmdGetResp( 1,
                              Pro2Cmd,
                              SI446X_CMD_REPLY_COUNT_GET_MODEM_STATUS,
                              Pro2Cmd );

    Si446xCmd.GET_MODEM_STATUS.MODEM_PEND   = Pro2Cmd[0];
    Si446xCmd.GET_MODEM_STATUS.MODEM_STATUS = Pro2Cmd[1];
    Si446xCmd.GET_MODEM_STATUS.CURR_RSSI    = Pro2Cmd[2];
    Si446xCmd.GET_MODEM_STATUS.LATCH_RSSI   = Pro2Cmd[3];
    Si446xCmd.GET_MODEM_STATUS.ANT1_RSSI    = Pro2Cmd[4];
    Si446xCmd.GET_MODEM_STATUS.ANT2_RSSI    = Pro2Cmd[5];
    Si446xCmd.GET_MODEM_STATUS.AFC_FREQ_OFFSET = ((U16)Pro2Cmd[6] << 8) & 0xFF00;
    Si446xCmd.GET_MODEM_STATUS.AFC_FREQ_OFFSET |= (U16)Pro2Cmd[7] & 0x00FF;
}

/*!
 * Clear all Chip status flags. Does NOT read back interrupt flags
 *
 */
void si446x_get_chip_status_fast_clear( void )
{
    Pro2Cmd[0] = SI446X_CMD_ID_GET_CHIP_STATUS;
    Pro2Cmd[1] = 0;

    radio_comm_SendCmd( 2, Pro2Cmd );
}

/*!
 * Clear and read all Chip status flags.
 *
 */
void si446x_get_chip_status_fast_clear_read( void )
{
    Pro2Cmd[0] = SI446X_CMD_ID_GET_CHIP_STATUS;

    radio_comm_SendCmdGetResp( 1,
                              Pro2Cmd,
                              SI446X_CMD_REPLY_COUNT_GET_CHIP_STATUS,
                              Pro2Cmd );

    Si446xCmd.GET_CHIP_STATUS.CHIP_PEND         = Pro2Cmd[0];
    Si446xCmd.GET_CHIP_STATUS.CHIP_STATUS       = Pro2Cmd[1];
    Si446xCmd.GET_CHIP_STATUS.CMD_ERR_STATUS    = Pro2Cmd[2];
}

/*!
 * Resets the RX/TX FIFO. Does not read back anything from TX/RX FIFO
 *
 */
void si446x_fifo_info_fast_reset(U8 FIFO)
{
    Pro2Cmd[0] = SI446X_CMD_ID_FIFO_INFO;
    Pro2Cmd[1] = FIFO;

    radio_comm_SendCmd( 2, Pro2Cmd );
}

/*!
 * Reads RX/TX FIFO count space. Does NOT reset RX/TX FIFO
 *
 */
void si446x_fifo_info_fast_read(void)
{
    Pro2Cmd[0] = SI446X_CMD_ID_FIFO_INFO;

    radio_comm_SendCmdGetResp( 1,
                              Pro2Cmd,
                              SI446X_CMD_REPLY_COUNT_FIFO_INFO,
                              Pro2Cmd );

    Si446xCmd.FIFO_INFO.RX_FIFO_COUNT   = Pro2Cmd[0];
    Si446xCmd.FIFO_INFO.TX_FIFO_SPACE   = Pro2Cmd[1];
}

#endif /* RADIO_DRIVER_FULL_SUPPORT */

#endif /* RADIO_DRIVER_EXTENDED_SUPPORT */
